ealauer/Animatronic_Research/Circuit Diagram Final/Circtuit Digram Camera.png

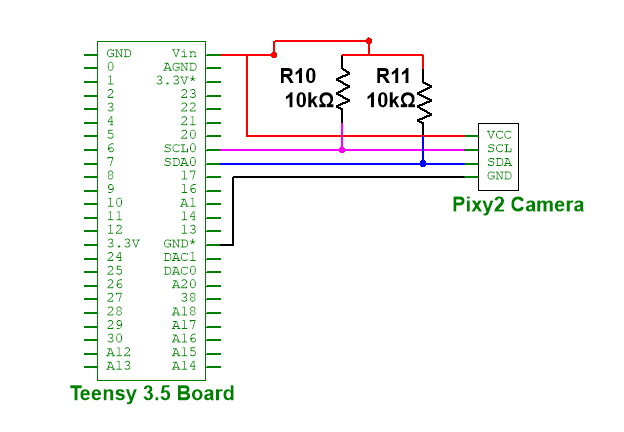
Circuit Diagram Final/Circtuit Digram Camera.png
