ealauer/Animatronic_Research/Circuit Diagram Final/Circuit Diagram FSR.png

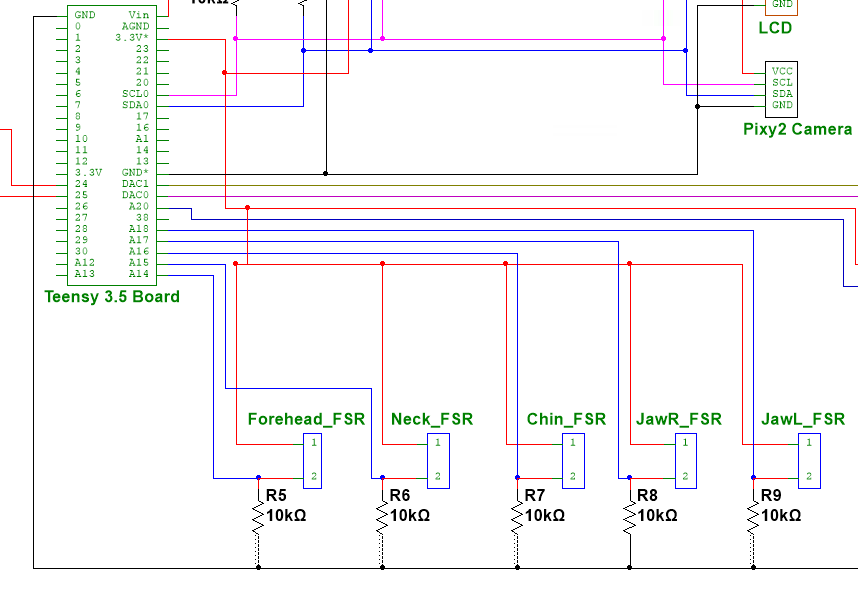
Circuit Diagram Final/Circuit Diagram FSR.png
