ealauer/Animatronic_Research/Circuit Diagram Final/Circuit Diagram Full1.png

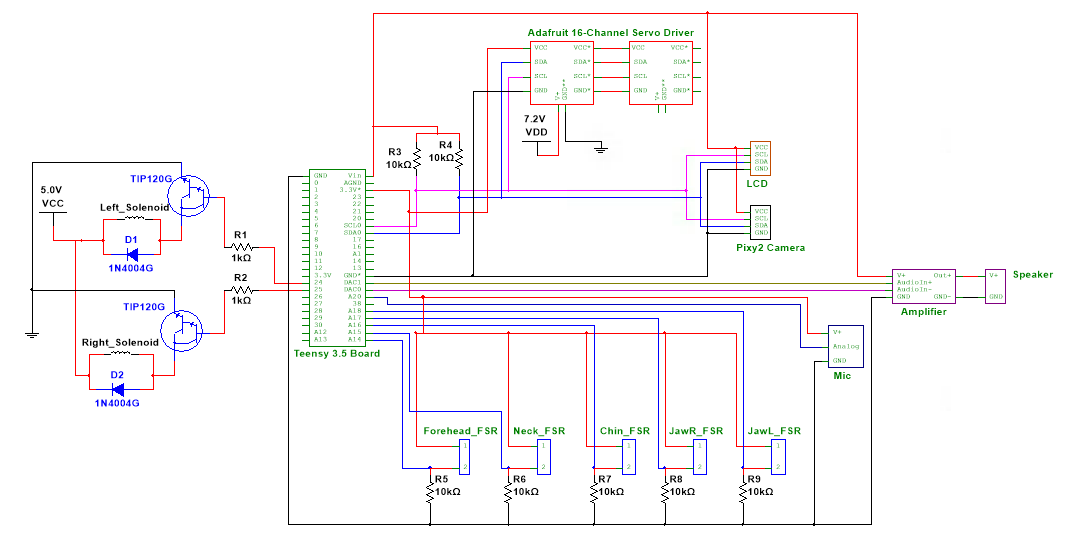
Circuit Diagram Final/Circuit Diagram Full1.png
