ealauer/Animatronic_Research/Circuit Diagram Final/Circuit Diagram I2C.png

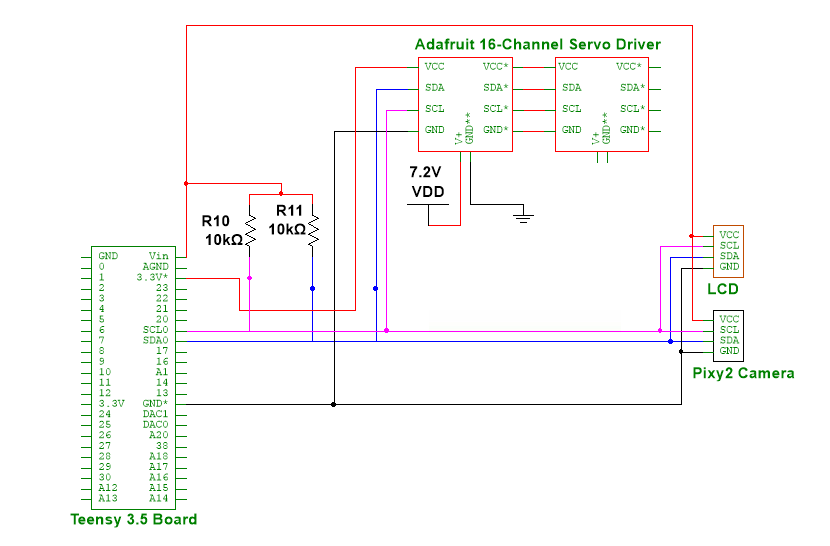
Circuit Diagram Final/Circuit Diagram I2C.png
