ealauer/Animatronic_Research/Circuit Diagram Final/Circuit Diagram LCD.png

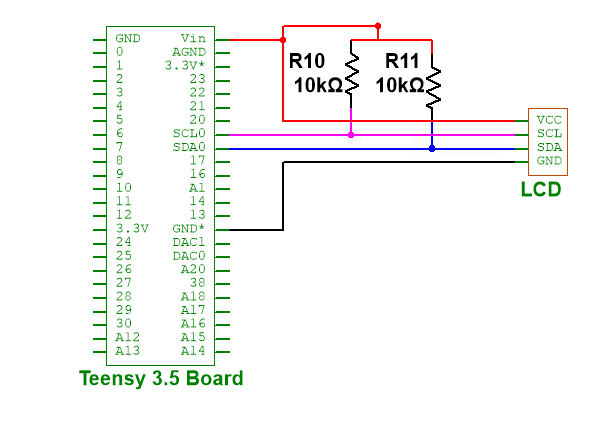
Circuit Diagram Final/Circuit Diagram LCD.png
