ealauer/Animatronic_Research/Circuit Diagram Final/Circuit Diagram MIC.png

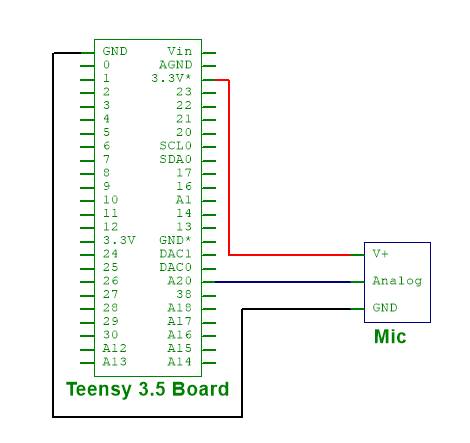
Circuit Diagram Final/Circuit Diagram MIC.png
