ealauer/Animatronic_Research/Circuit Diagram Final/Circuit Diagram Pulse.png

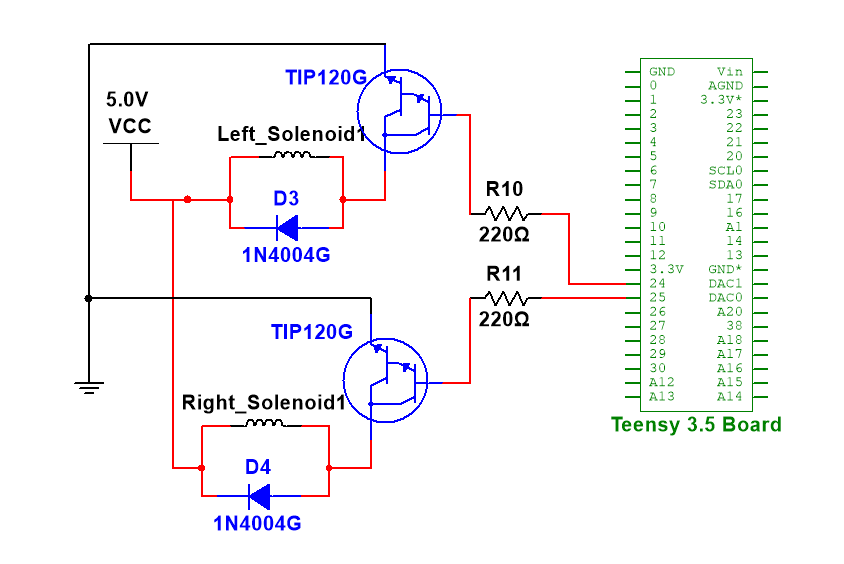
Circuit Diagram Final/Circuit Diagram Pulse.png
