ealauer/Animatronic_Research/Circuit Diagram Final/Circuit Diagram Servo.png

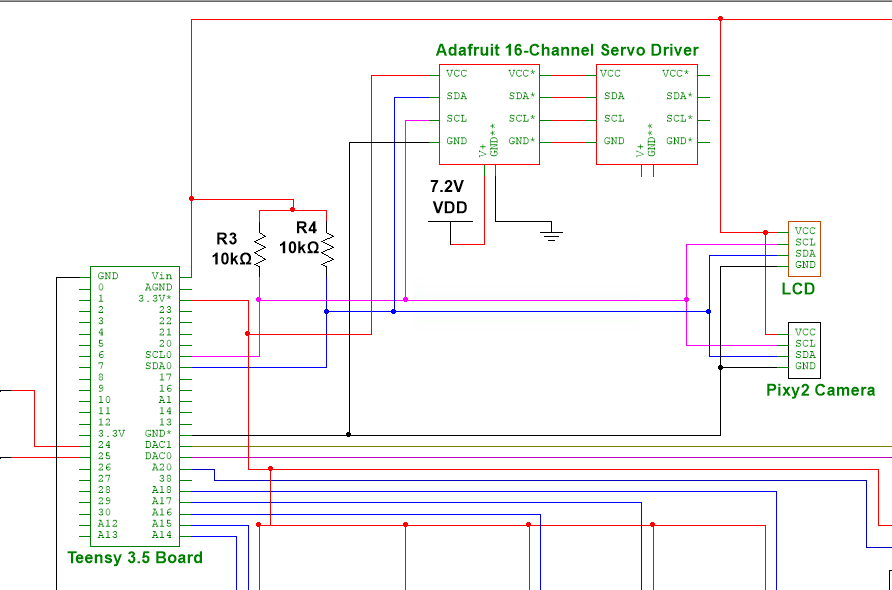
Circuit Diagram Final/Circuit Diagram Servo.png
