ealauer/Animatronic_Research/Circuit Diagram Final/Circuit Diagram Speaker.png

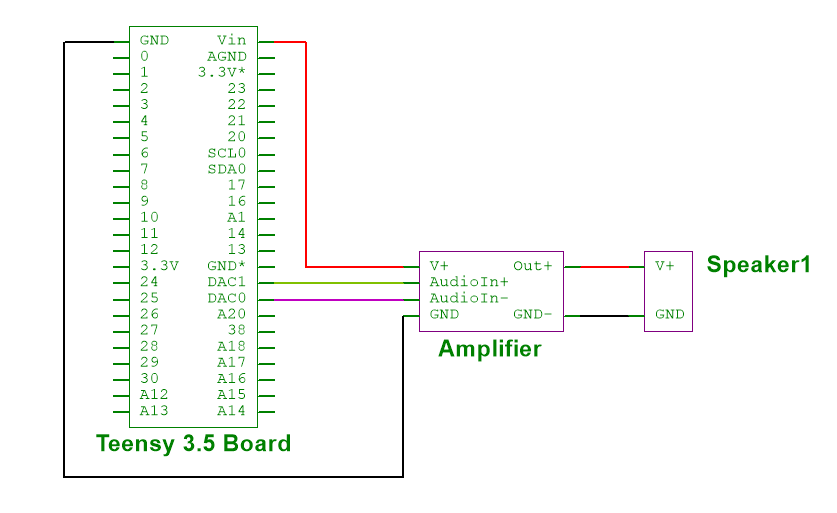
Circuit Diagram Final/Circuit Diagram Speaker.png
