ealauer/Animatronic_Research/MATLAB/figLegLengthWXPoseNew.png

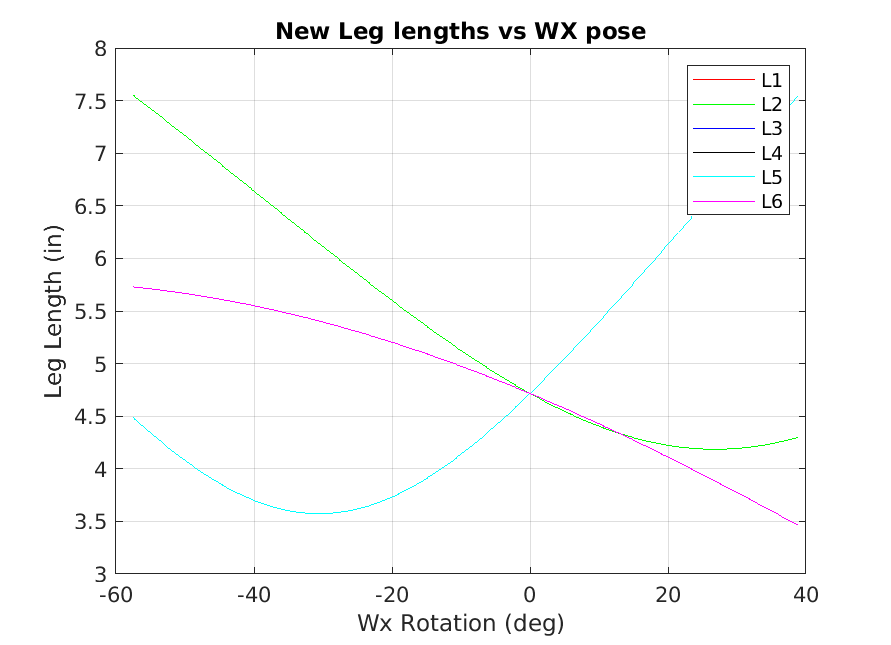
MATLAB/figLegLengthWXPoseNew.png
