ealauer/Animatronic_Research/MATLAB/figLegLengthWYPoseNew.png

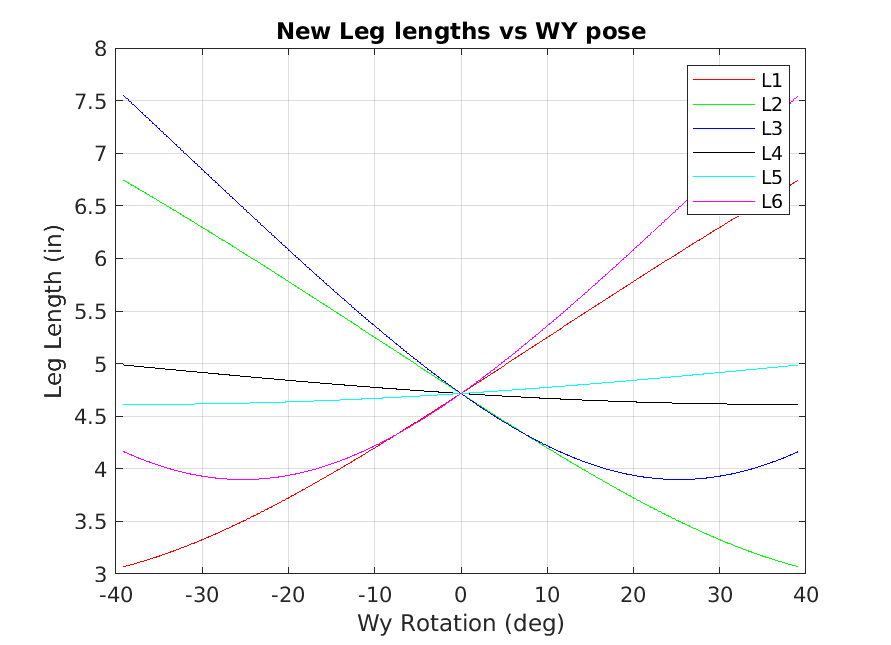
MATLAB/figLegLengthWYPoseNew.png
