ealauer/Animatronic_Research/MATLAB/figLegLengthWZPose.png

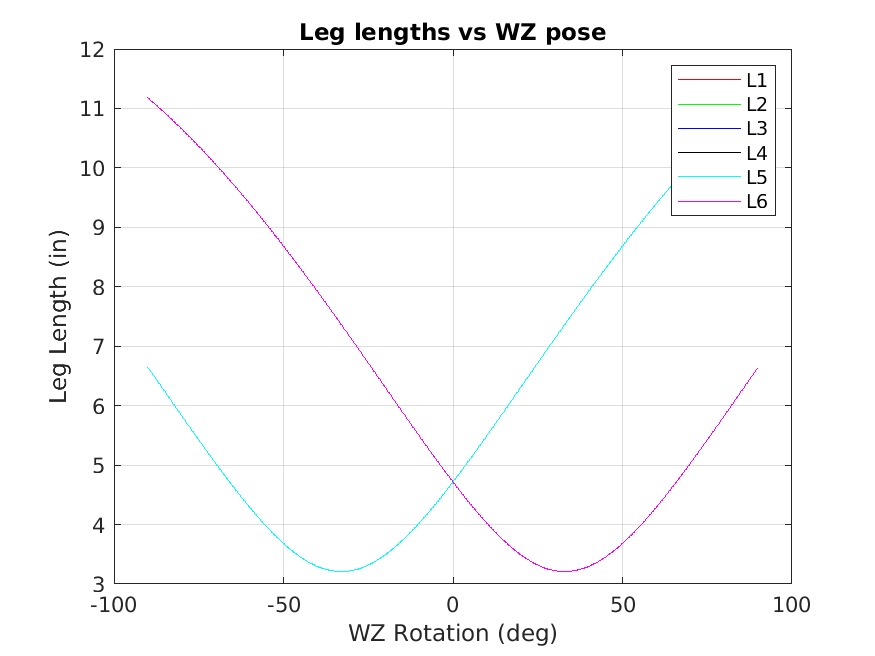
MATLAB/figLegLengthWZPose.png
