ealauer/Animatronic_Research/MATLAB/figLegLengthWZPoseNew.png

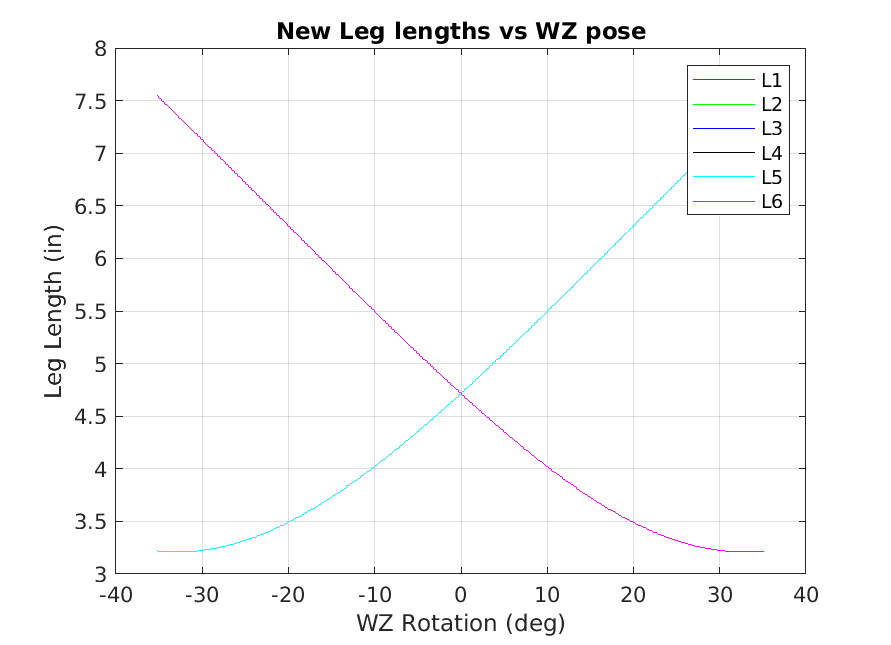
MATLAB/figLegLengthWZPoseNew.png
