ealauer/Animatronic_Research/MATLAB/figLegLengthZPose.png

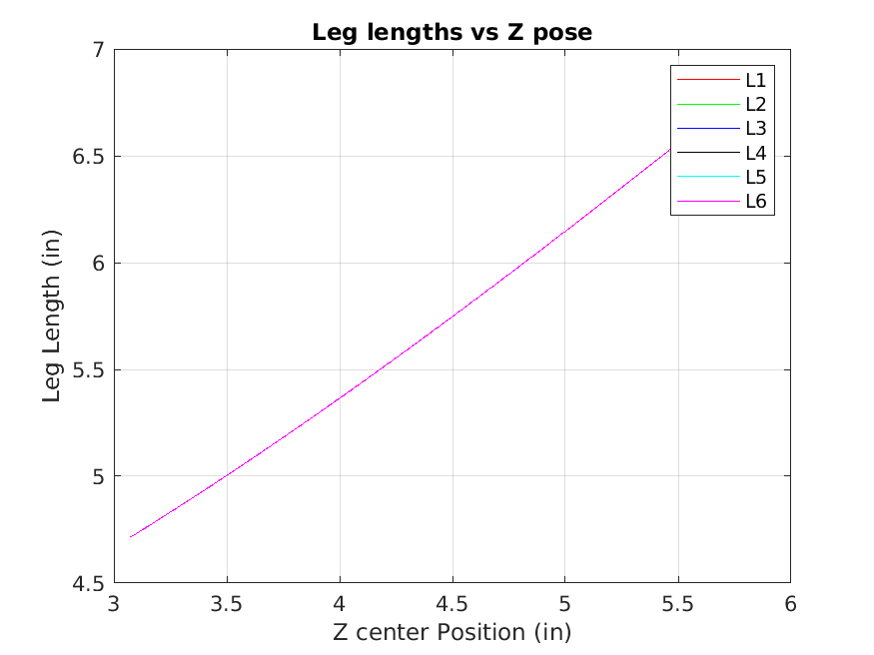
MATLAB/figLegLengthZPose.png
