ealauer/Animatronic_Research/MATLAB/figLegLengthZPoseNew.png

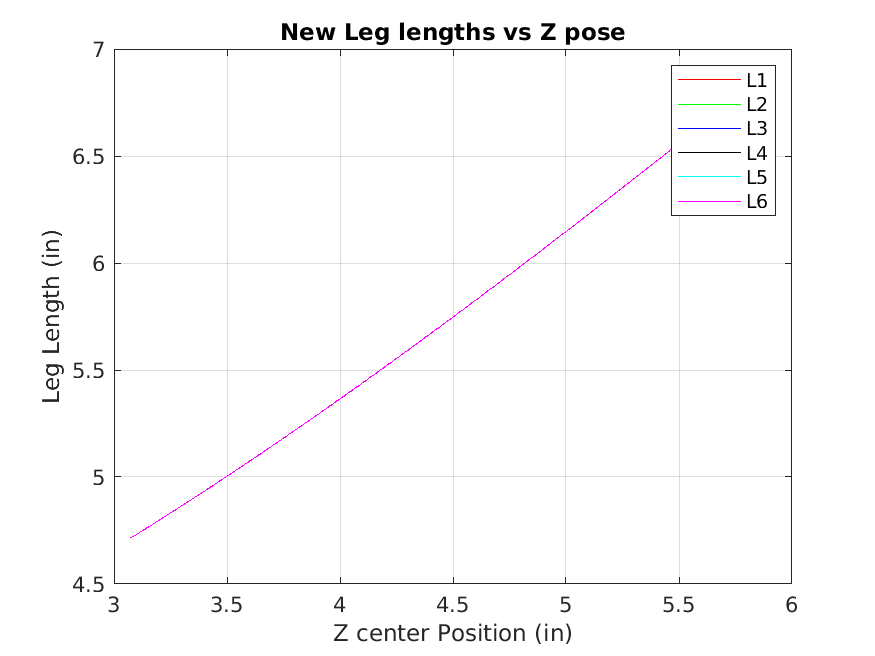
MATLAB/figLegLengthZPoseNew.png
