ealauer/Animatronic_Research/MATLAB/figServoWXPose.png

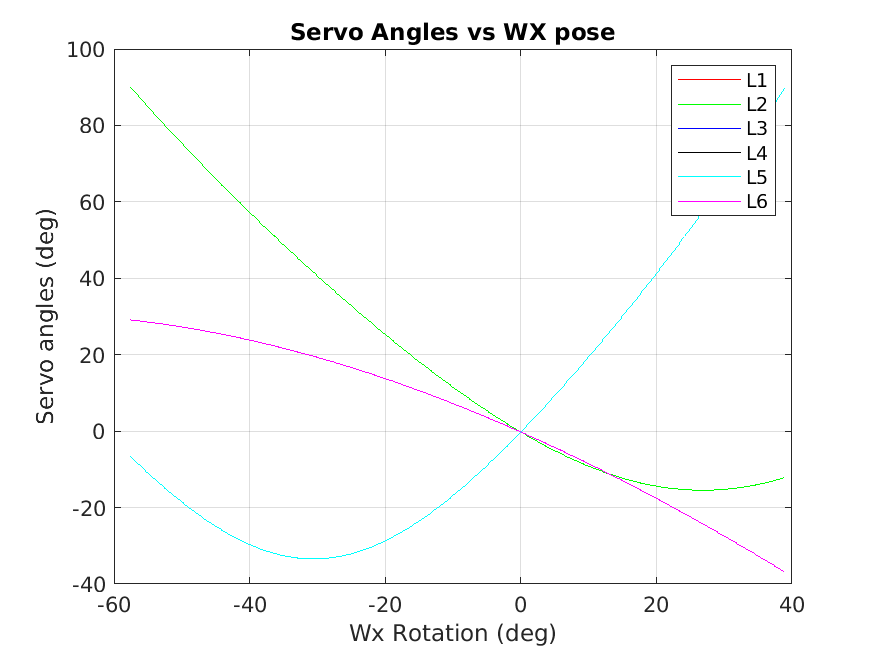
MATLAB/figServoWXPose.png
