ealauer/Animatronic_Research/MATLAB/figServoWYPose.png

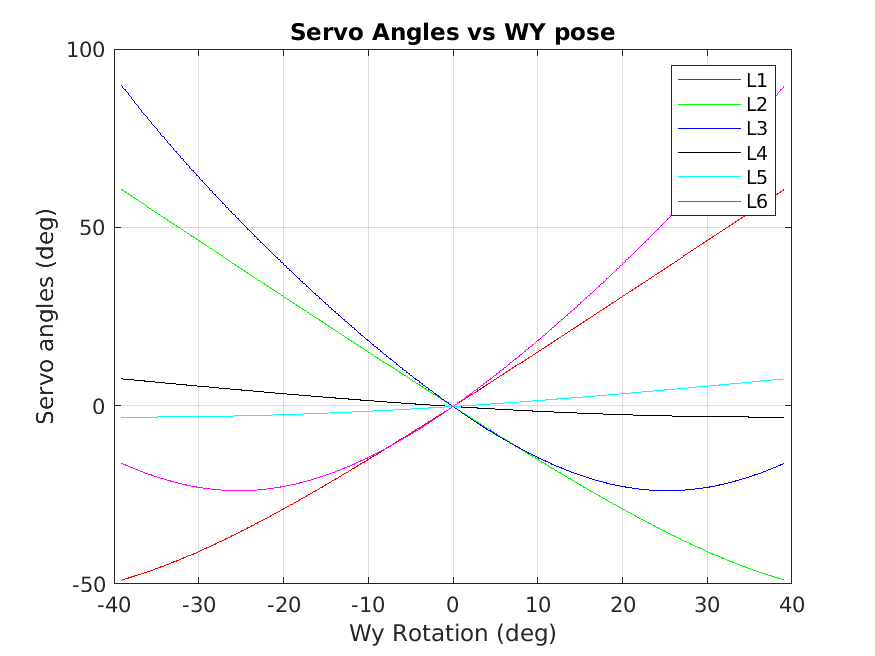
MATLAB/figServoWYPose.png
