ealauer/Animatronic_Research/MATLAB/figServoWZPose.png

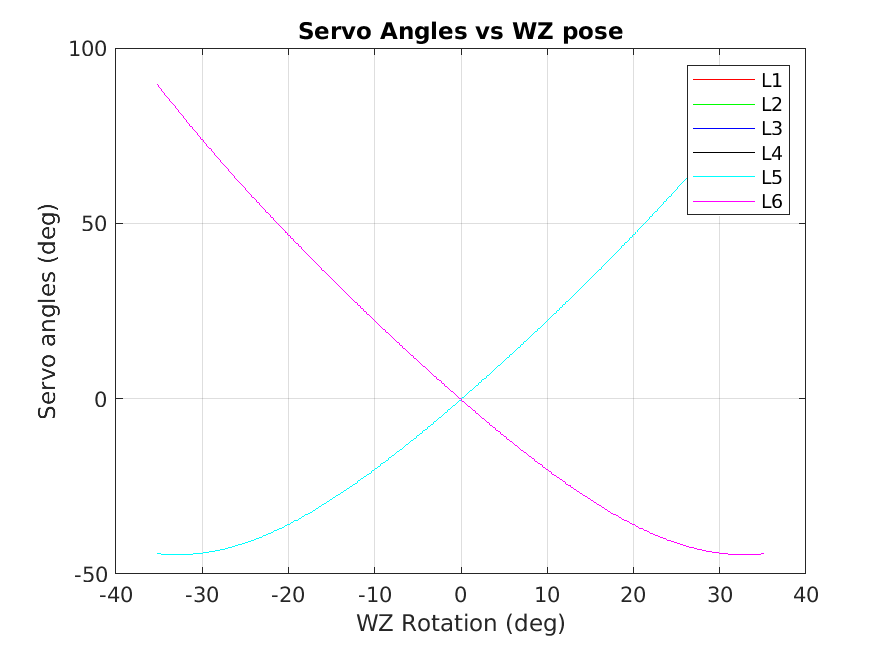
MATLAB/figServoWZPose.png
