ealauer/Animatronic_Research/UI Flow Pictures/2LOC.jpg

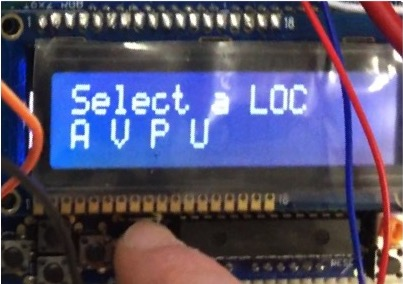
UI Flow Pictures/2LOC.jpg
