ealauer/Animatronic_Research/UI Flow Pictures/3LOCSet.jpg

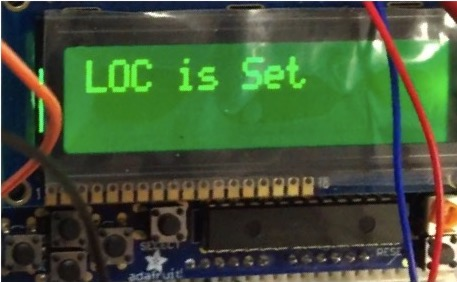
UI Flow Pictures/3LOCSet.jpg
