ealauer/Animatronic_Research/UI Flow Pictures/4Air.jpg

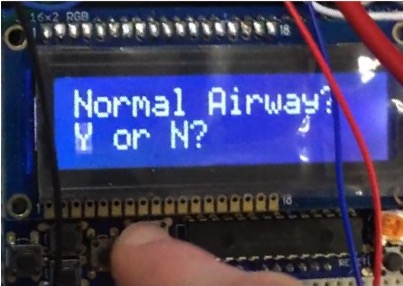
UI Flow Pictures/4Air.jpg
