ealauer/Animatronic_Research/UI Flow Pictures/7PulseInput.jpg

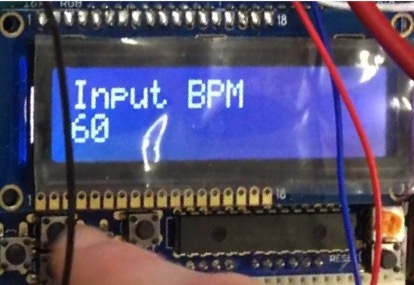
UI Flow Pictures/7PulseInput.jpg
