ealauer/Animatronic_Research/UI Flow Pictures/8PulseSet.jpg

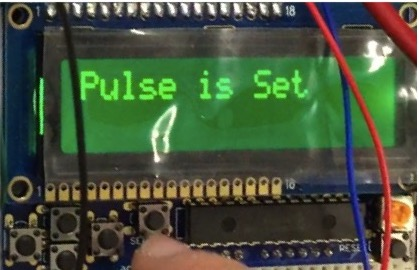
UI Flow Pictures/8PulseSet.jpg
