ealauer/Animatronic_Research/UI Flow Pictures/10StartQues.jpg

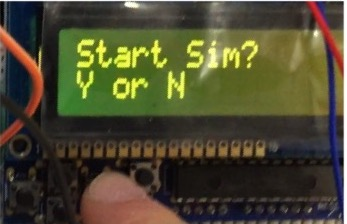
UI Flow Pictures/10StartQues.jpg
