ealauer/Animatronic_Research/UI Flow Pictures/11Change.jpg

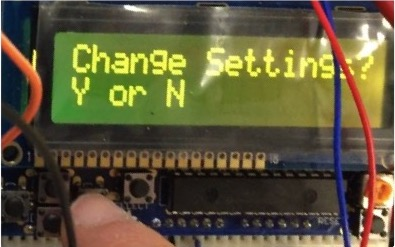
UI Flow Pictures/11Change.jpg
