ealauer/Animatronic_Research/UI Flow Pictures/12Start.jpg

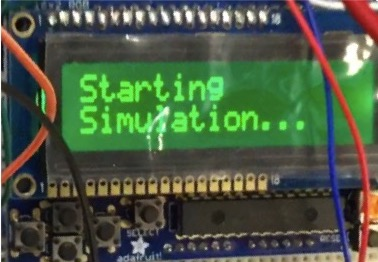
UI Flow Pictures/12Start.jpg
