ealauer/Animatronic_Research/SolidWorks Files/march16 eyebrow.SLDASM

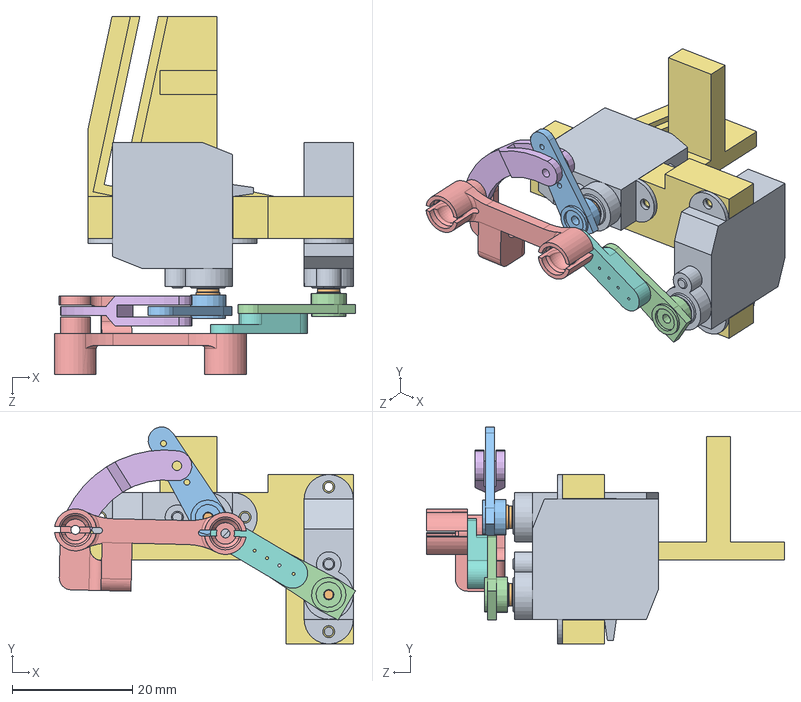
[picture p47: CAD file, 2021-04-09]
SolidWorks Files/march16 eyebrow.SLDASM
50.1 x 36.1 x 59.6 mm
D56MG Servo Case (1) x 2
D56MG Servo Shaft x 2
drilled and trimmed servo horn
Servo horn trimmed
brow link v2
middle link eyebrow v2
v9 eyebrowbaseleft
20mm extension link
