ealauer/Animatronic_Research/SolidWorks Files/Jaw/Jaw Thrust Linkage/LinkageAssemWithServoRight.SLDASM

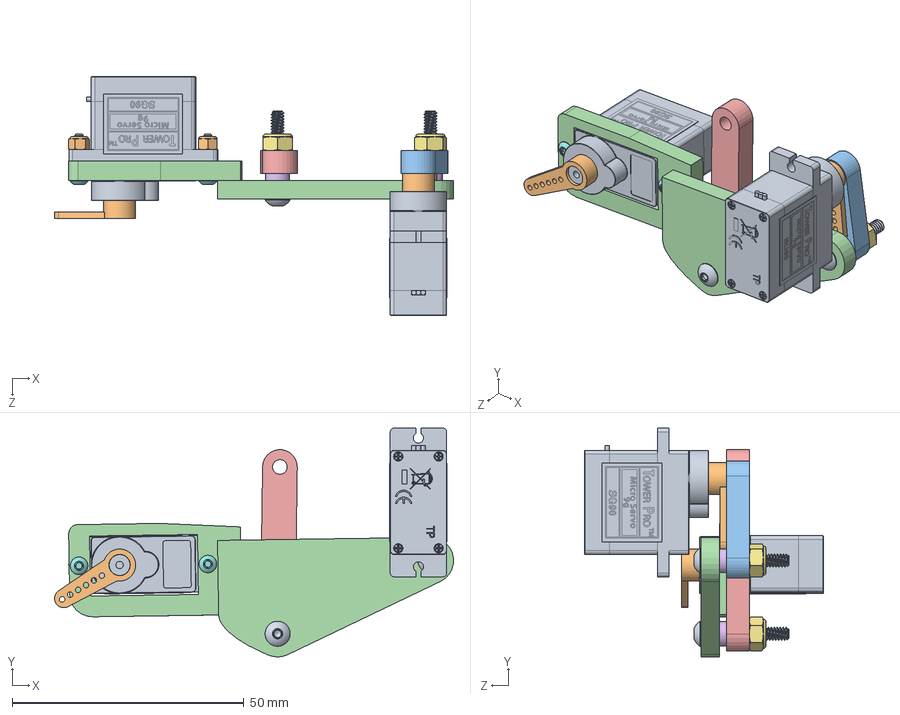
[picture p48: CAD file, 2021-04-09]
SolidWorks Files/Jaw/Jaw Thrust Linkage/LinkageAssemWithServoRight.SLDASM
86.1 x 49.4 x 51.7 mm
SG90 - Micro Servo 9g - Tower Pro.1 x 2
SG90 - Micro Servo 9g - Tower Pro.2 x 2
Driving
TriangleEditedRight
Driven2
90295A341_NYLON FLAT WASHER x 2
91831A005_TYPE 18-8 STAINLESS STL NYLON-INSERT LOCKNUT x 2
92095A104_BUTTON HEAD HEX DRIVE SCREW x 2
92949A113_18-8 SS BUTTON HEAD HEX DRIVE SCREW x 2
93625A101_TYPE 18-8 STAINLESS STL NYLON-INSERT LOCKNUT x 2
