ealauer/Animatronic_Research/SolidWorks Files/Eye CAD/Eye Assembly Final.SLDASM

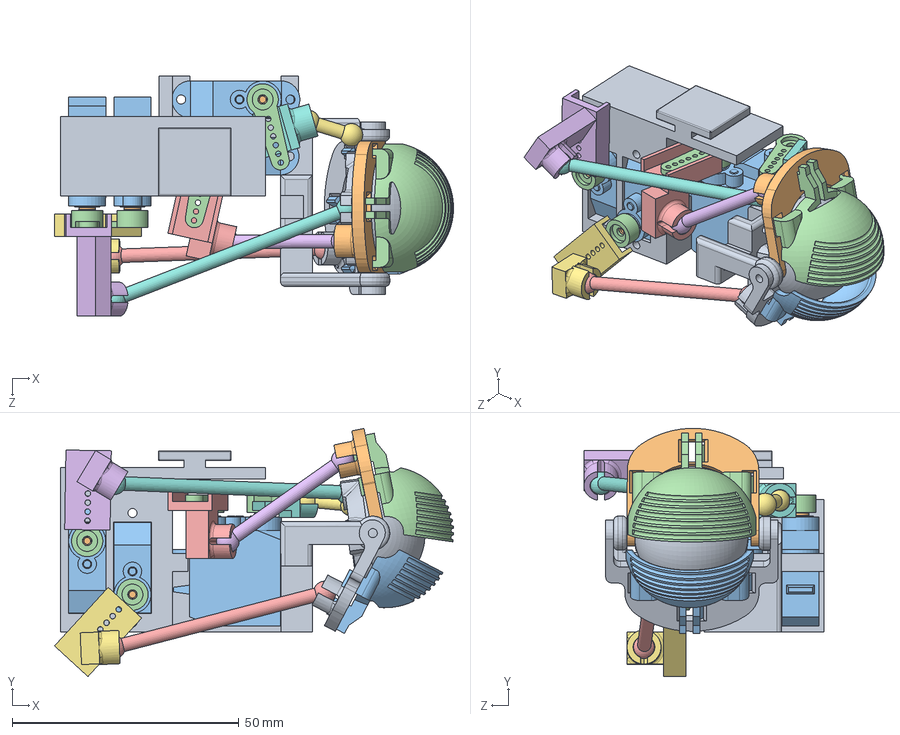
[picture p49: CAD file, 2021-04-09]
SolidWorks Files/Eye CAD/Eye Assembly Final.SLDASM
87.9 x 54.7 x 52.9 mm
final_eye_holder_V3.75_final
D56MG Servo Shaft x 4
D56MG Servo Case (1) x 4
SG90 - Micro Servo 9g - Tower Pro.2 x 4
final_servo_ball_joint_link4
final_servo_ball_joint_link3
final_servo_ball_joint_link2
final_servo_ball_joint_link1
final_eye clip butterfly bottom
final_eye clip butterfly top
final_clip on eyelid rev3
final_clip on eyelid top rev3
final_link1
final_link3
final_link4
final_link2
final eyeball
