ealauer/Animatronic_Research/SolidWorks Files/Neck/Neck Mechanism/Neck Lattice Assembly.SLDASM

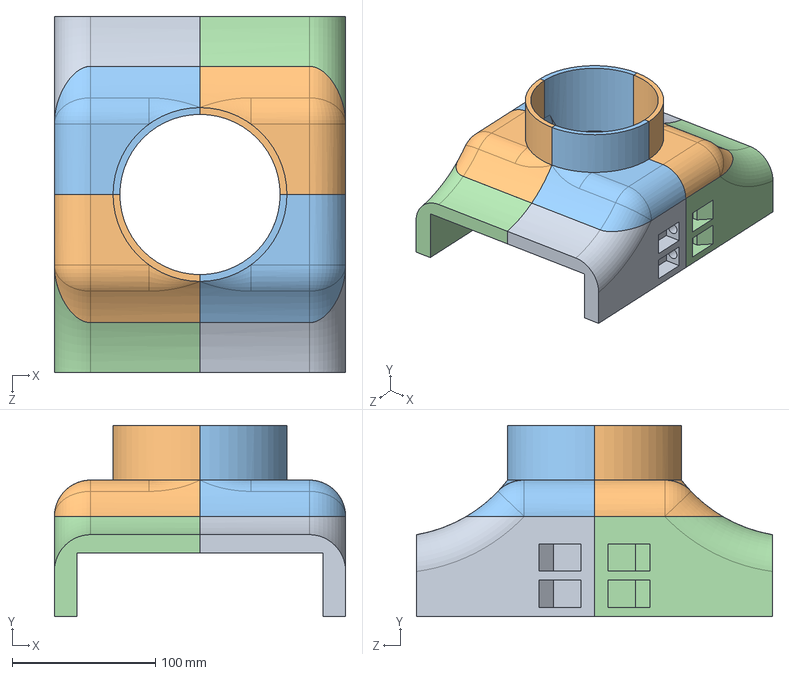
[picture p50: CAD file, 2021-04-09]
SolidWorks Files/Neck/Neck Mechanism/Neck Lattice Assembly.SLDASM
203.2 x 133.4 x 248.3 mm
Neck Sizing Bottom Female x 2
Neck Sizing Top FemaleMale x 2
Neck Sizing Top MaleMale x 2
Neck Sizing Bottom Male x 2
