ealauer/Animatronic_Research/SolidWorks Files/Eye Assembly.SLDASM

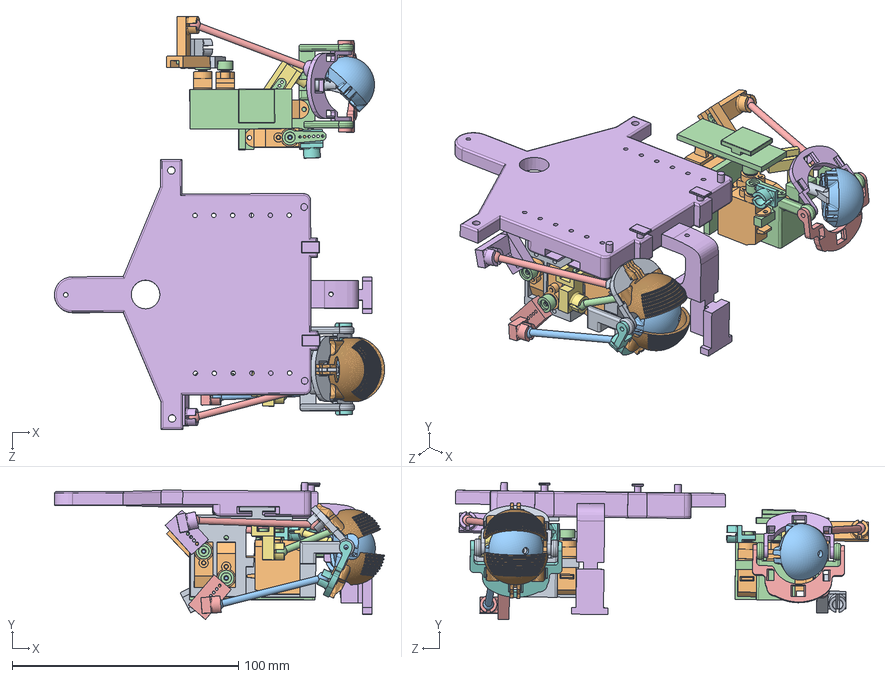
[picture p51: CAD file, 2021-04-09]
SolidWorks Files/Eye Assembly.SLDASM
146.1 x 60.7 x 182.7 mm
final_eye_holder_V3.75_final
D56MG Servo Case (1) x 8
D56MG Servo Shaft x 8
SG90 - Micro Servo 9g - Tower Pro.2 x 8
final_servo_ball_joint_link2
final_servo_ball_joint_link3
final_servo_ball_joint_link4
final_servo_ball_joint_link1
Ball Joint case x 2
Ball joint ball x 2
final_link1
final_link3
final_link2 x 2
platform_V3 (2)
new link
final_eye clip butterfly bottom
final_eye clip butterfly top
final_clip on eyelid top rev3 x 2
final eyeball_lauer x 2
final_left_eye_holder_lauer
final_left_eye clip butterfly bottom
final_left_eye clip butterfly top
final_left_servo_ball_joint_link4
final_left_servo_ball_joint_link1
final_left_servo_ball_joint_link2
final_left_servo_ball_joint_link3
