ealauer/Animatronic_Research/SolidWorks Files/Base Assembly.SLDASM

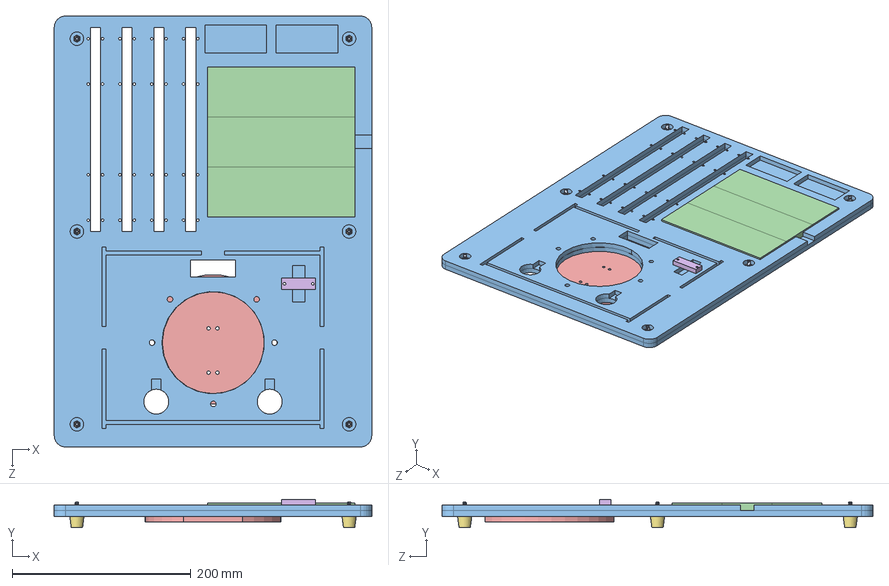
[picture p52: CAD file, 2021-04-09]
SolidWorks Files/Base Assembly.SLDASM
355.6 x 31.8 x 482.6 mm
90128A216_ZNC-PLTD ALLOY STL SCKT HEAD CAP SCREW x 6
90592A090_STEEL HEX NUT x 6
Base x 2
breadboard Updated x 3
Botttom Support
Cover
Stands x 6
