ealauer/Animatronic_Research/SolidWorks Files/D56MG Servo Assembly.SLDASM

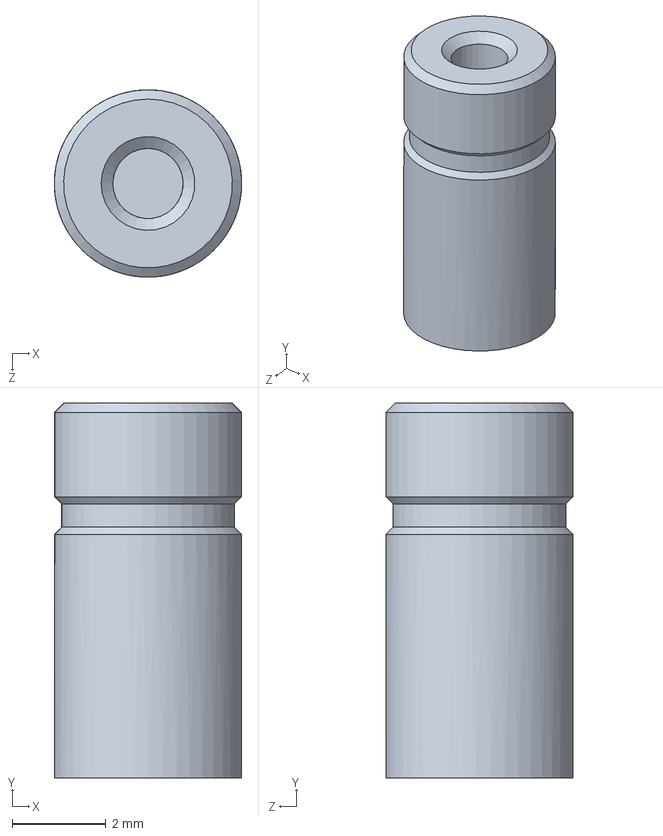
[picture p53: CAD file, 2021-04-09]
SolidWorks Files/D56MG Servo Assembly.SLDASM
4.00 x 8.00 x 4.00 mm
