ealauer/Animatronic_Research/SolidWorks Files/Eye CAD/final_eye clip butterfly bottom.SLDPRT

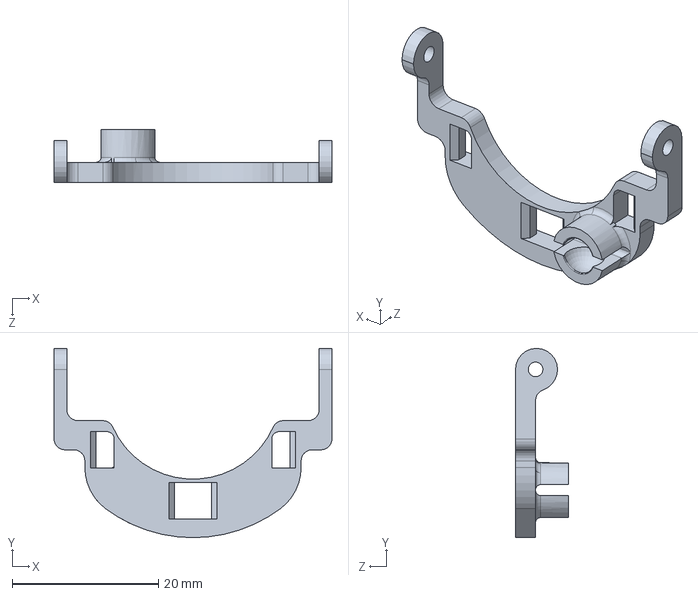
[picture p54: CAD file, 2021-04-09]
SolidWorks Files/Eye CAD/final_eye clip butterfly bottom.SLDPRT
38.0 x 25.9 x 7.25 mm
