ealauer/Animatronic_Research/SolidWorks Files/Eyebrows/Left Eyebrow/D56MG Servo Case.SLDPRT

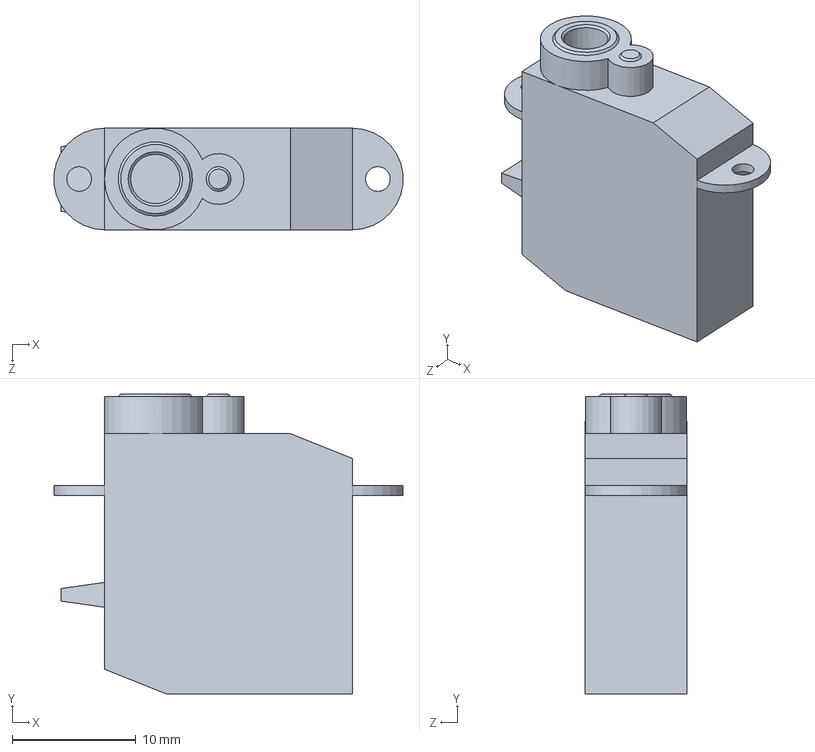
[picture p55: CAD file, 2021-04-09]
SolidWorks Files/Eyebrows/Left Eyebrow/D56MG Servo Case.SLDPRT
28.2 x 24.2 x 8.20 mm
