ealauer/Animatronic_Research/SolidWorks Files/Eyebrows/Left Eyebrow/Left .stl_s/brow link v2.STL

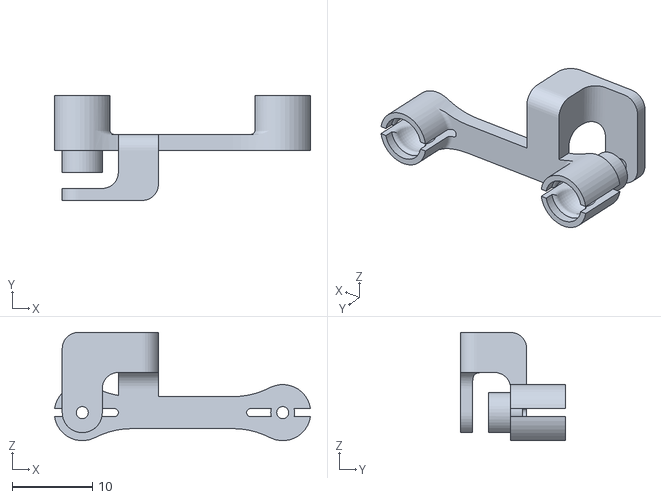
[picture p56: CAD file, 2021-04-09]
SolidWorks Files/Eyebrows/Left Eyebrow/Left .stl_s/brow link v2.STL
31.9 x 13.1 x 13.5
