ealauer/Animatronic_Research/SolidWorks Files/Eyebrows/Right Eyebrow/Right .stl_s/R_20mm extension link.STL

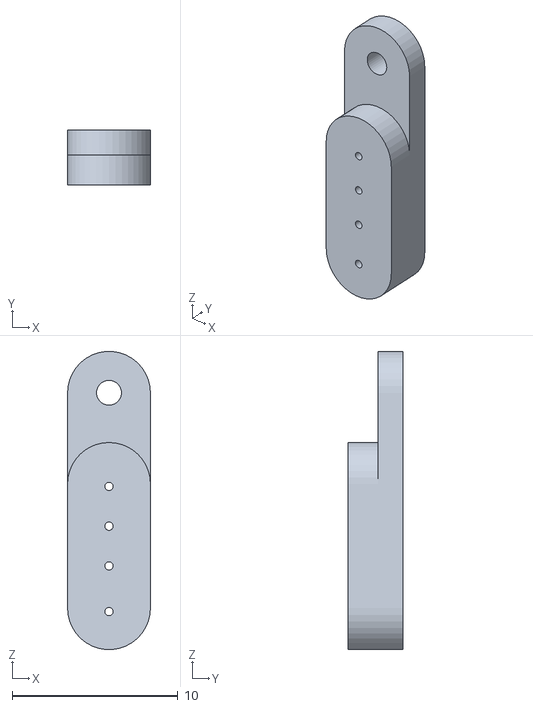
[picture p57: CAD file, 2021-04-09]
SolidWorks Files/Eyebrows/Right Eyebrow/Right .stl_s/R_20mm extension link.STL
5.00 x 3.30 x 18.0
