ealauer/Animatronic_Research/SolidWorks Files/final_servo_ball_joint_link1.SLDPRT

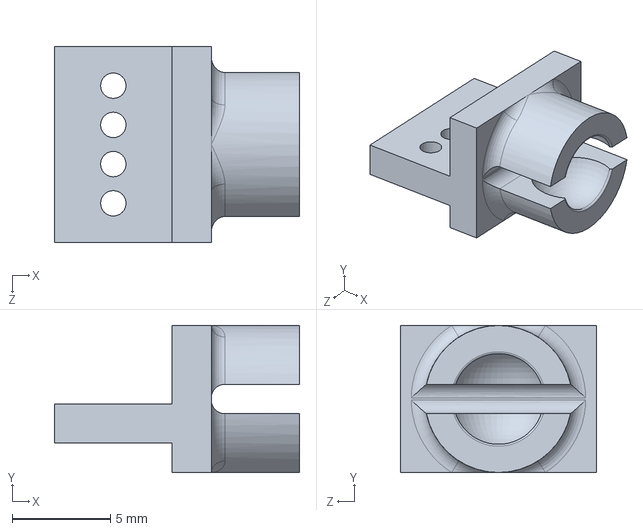
[picture p58: CAD file, 2021-04-09]
SolidWorks Files/final_servo_ball_joint_link1.SLDPRT
12.5 x 7.50 x 10.0 mm
