ealauer/Animatronic_Research/SolidWorks Files/Jaw/Oral Roof.SLDPRT

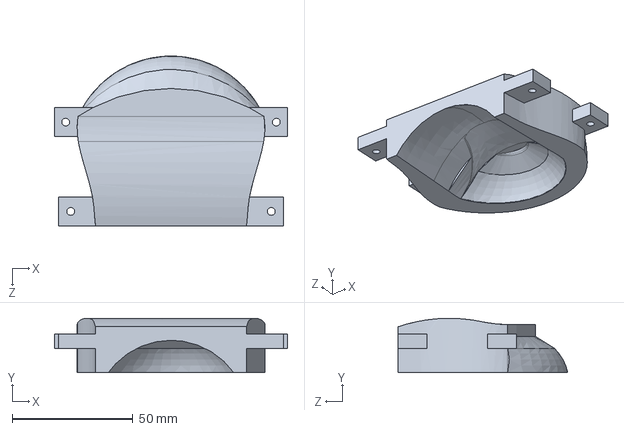
[picture p59: CAD file, 2021-04-09]
SolidWorks Files/Jaw/Oral Roof.SLDPRT
96.6 x 22.5 x 70.4 mm
