ealauer/Animatronic_Research/SolidWorks Files/Neck/Neck Enclosure/Cover.SLDPRT

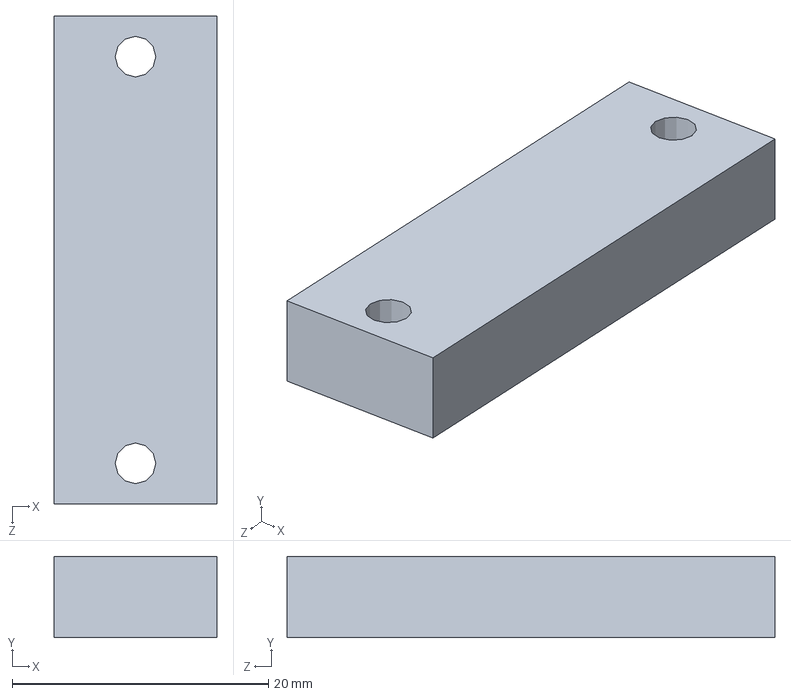
[picture p60: CAD file, 2021-04-09]
SolidWorks Files/Neck/Neck Enclosure/Cover.SLDPRT
12.7 x 6.35 x 38.1 mm
