ealauer/Animatronic_Research/SolidWorks Files/Neck/Neck Mechanism/Servo Linkage1.SLDPRT

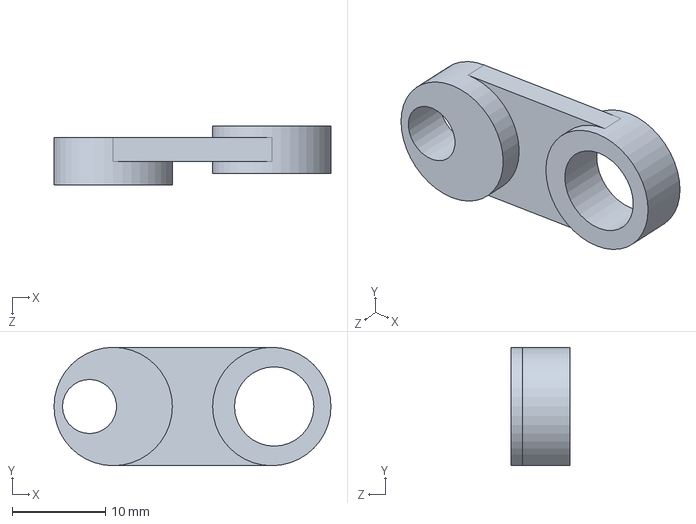
[picture p61: CAD file, 2021-04-09]
SolidWorks Files/Neck/Neck Mechanism/Servo Linkage1.SLDPRT
29.7 x 12.7 x 6.35 mm
