ealauer/Animatronic_Research/Stewart Platform Initial Designs/workspace modeling.SLDPRT

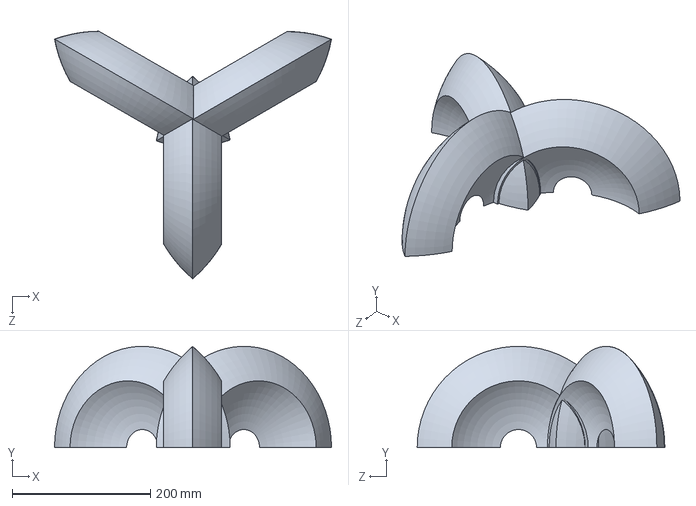
[picture p62: CAD file, 2021-04-09]
Stewart Platform Initial Designs/workspace modeling.SLDPRT
401.2 x 146.7 x 358.7 mm
