ealauer/Animatronic_Research/SolidWorks Files/Eyebrows/Left Eyebrow/Left .stl_s/v9 eyebrowbaseleft.STL

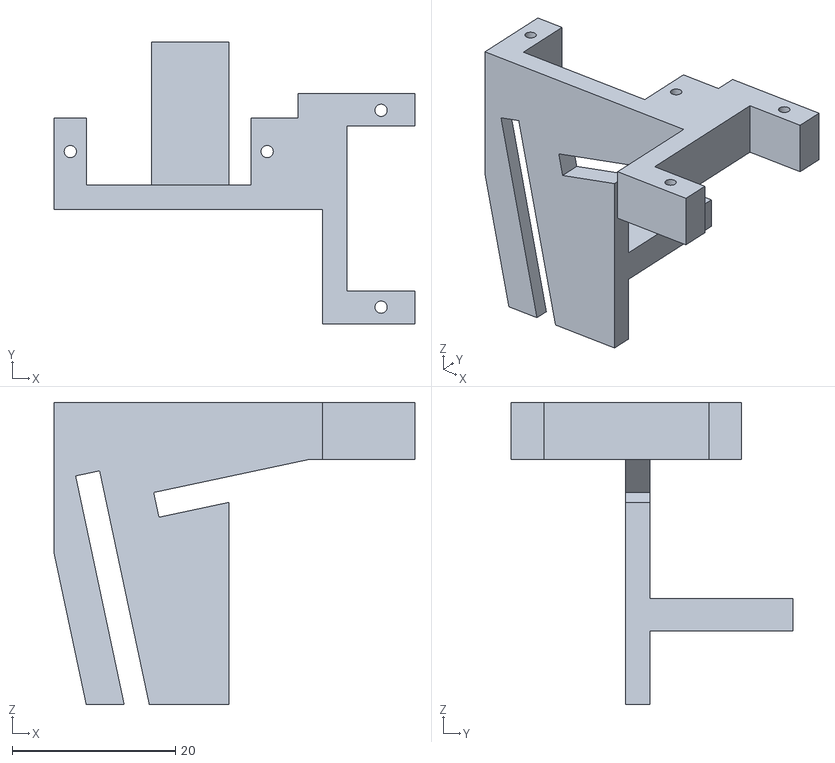
[picture p63: CAD file, 2021-04-09]
SolidWorks Files/Eyebrows/Left Eyebrow/Left .stl_s/v9 eyebrowbaseleft.STL
44.2 x 34.5 x 37.0
