ealauer/Animatronic_Research/SolidWorks Files/Gasket Rod.SLDPRT

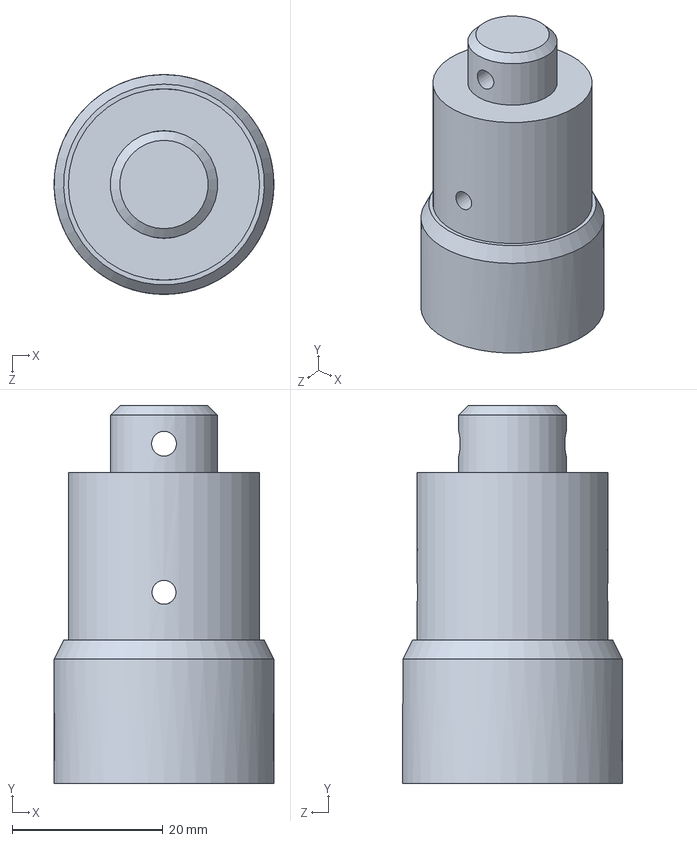
[picture p64: CAD file, 2021-04-09]
SolidWorks Files/Gasket Rod.SLDPRT
29.2 x 50.2 x 29.2 mm
