ealauer/Animatronic_Research/SolidWorks Files/Jaw/Jaw Thrust Linkage/Driven2.SLDPRT

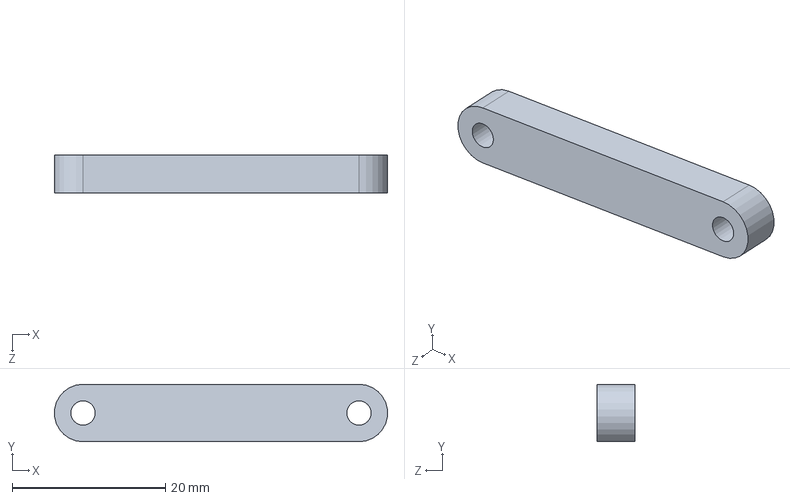
[picture p65: CAD file, 2021-04-09]
SolidWorks Files/Jaw/Jaw Thrust Linkage/Driven2.SLDPRT
43.4 x 7.50 x 5.00 mm
