ealauer/Animatronic_Research/SolidWorks Files/Neck/Neck Mechanism/Savr.SLDPRT

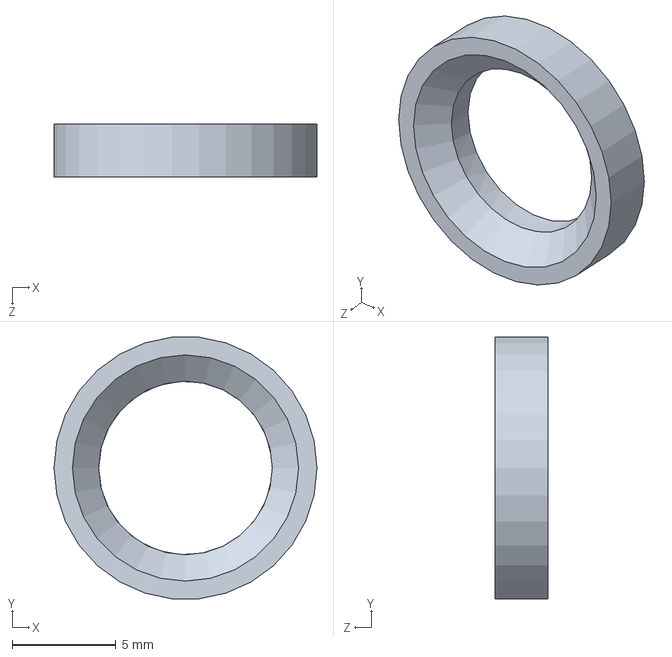
[picture p67: CAD file, 2021-04-09]
SolidWorks Files/Neck/Neck Mechanism/Savr.SLDPRT
12.7 x 12.6 x 2.54 mm
