ealauer/Animatronic_Research/Stewart Platform Initial Designs/platform_bot.dxf

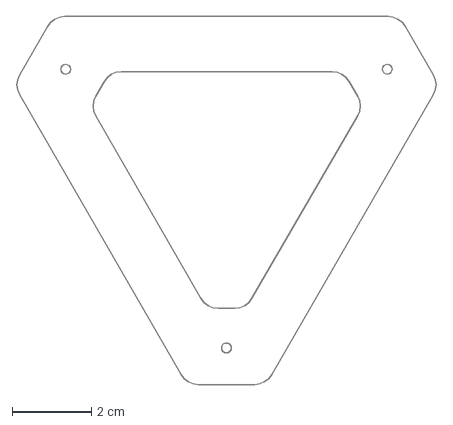
[picture p68: CAD file, 2021-04-09]
Stewart Platform Initial Designs/platform_bot.dxf
10.6 x 9.31 cm
