ealauer/Animatronic_Research/SolidWorks Files/Eyebrows/Left Eyebrow/Left .stl_s/middle link eyebrow v2.STL

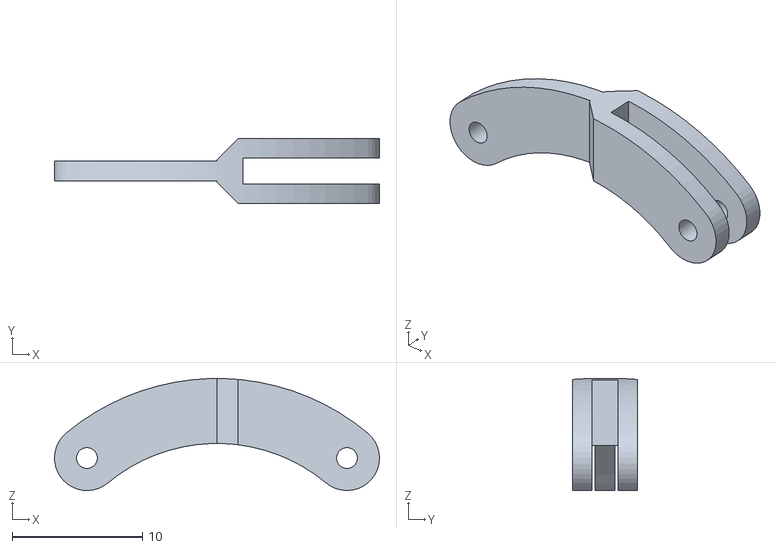
[picture p69: CAD file, 2021-04-09]
SolidWorks Files/Eyebrows/Left Eyebrow/Left .stl_s/middle link eyebrow v2.STL
25.0 x 5.00 x 8.62
