ealauer/Animatronic_Research/SolidWorks Files/Eyebrows/Left Eyebrow/Servo horn trimmed.SLDPRT

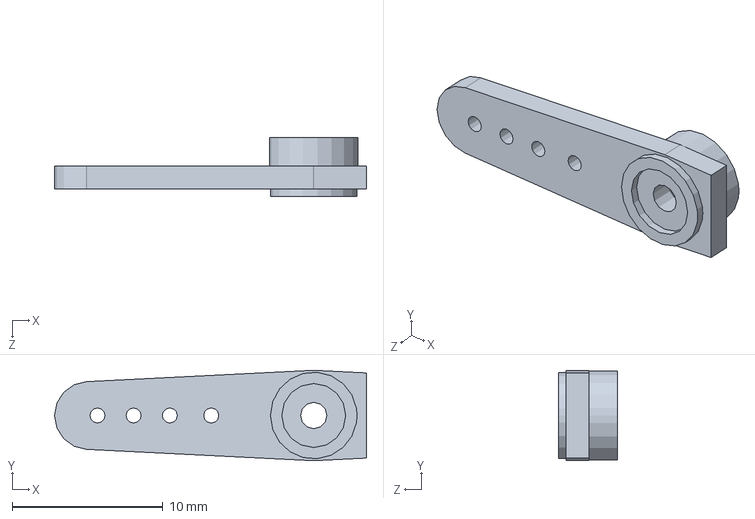
[picture p70: CAD file, 2021-04-09]
SolidWorks Files/Eyebrows/Left Eyebrow/Servo horn trimmed.SLDPRT
20.7 x 6.00 x 3.90 mm
