ealauer/Animatronic_Research/SolidWorks Files/Jaw/Jaw Thrust Linkage/Driving.SLDPRT

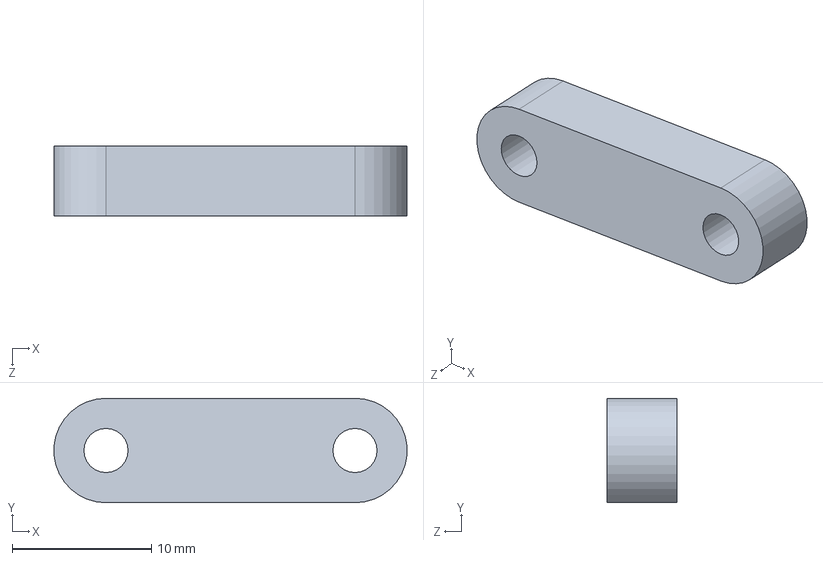
[picture p71: CAD file, 2021-04-09]
SolidWorks Files/Jaw/Jaw Thrust Linkage/Driving.SLDPRT
25.3 x 7.50 x 5.00 mm
