ealauer/Animatronic_Research/SolidWorks Files/Jaw/Tongue 2.SLDPRT

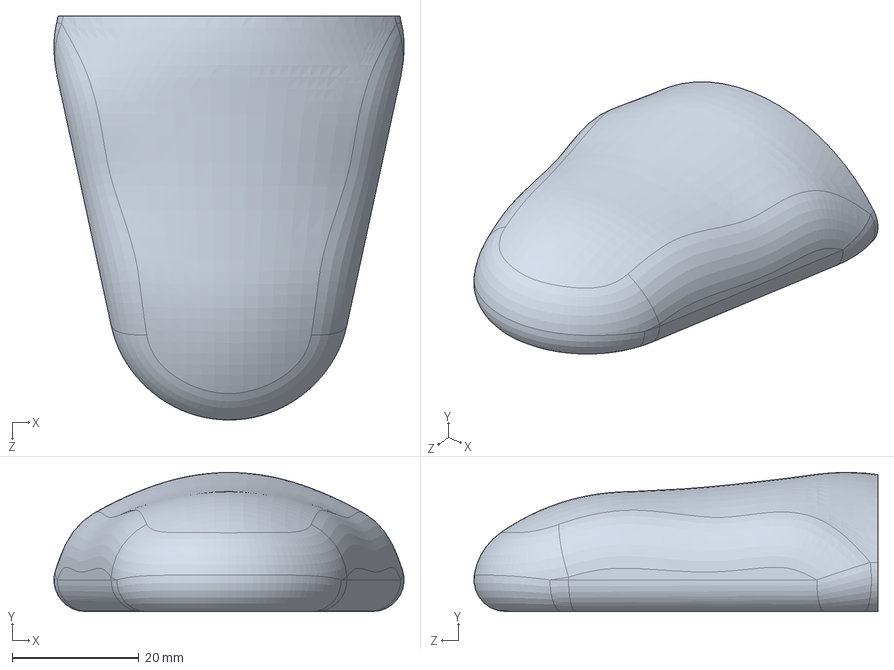
[picture p72: CAD file, 2021-04-09]
SolidWorks Files/Jaw/Tongue 2.SLDPRT
55.3 x 22.0 x 63.8 mm
