ealauer/Animatronic_Research/SolidWorks Files/Neck/Neck Enclosure/Top Actual.SLDPRT

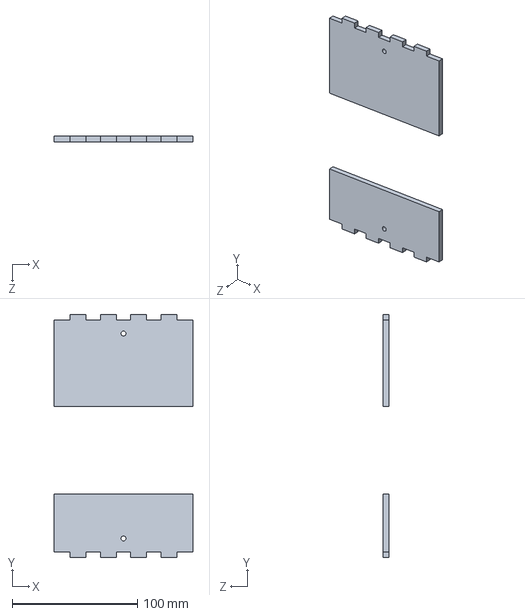
[picture p73: CAD file, 2021-04-09]
SolidWorks Files/Neck/Neck Enclosure/Top Actual.SLDPRT
110.9 x 194.2 x 4.50 mm
