ealauer/Animatronic_Research/SolidWorks Files/Neck/Neck Mechanism/Gasket to HeadNeck Interface Rod.SLDPRT

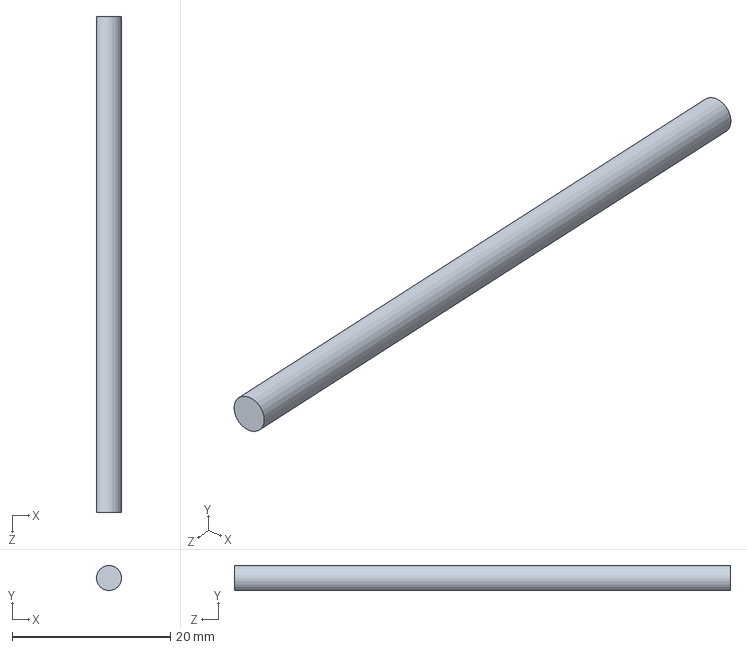
[picture p74: CAD file, 2021-04-09]
SolidWorks Files/Neck/Neck Mechanism/Gasket to HeadNeck Interface Rod.SLDPRT
3.17 x 3.17 x 62.7 mm
