ealauer/Animatronic_Research/Stewart Platform Initial Designs/platform_top.dxf

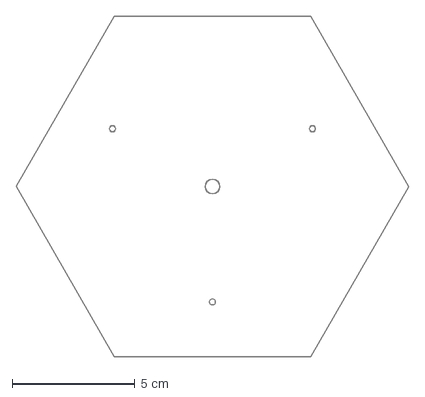
[picture p75: CAD file, 2021-04-09]
Stewart Platform Initial Designs/platform_top.dxf
16.0 x 13.9 cm
