ealauer/Animatronic_Research/SolidWorks Files/Eye CAD/final_clip on eyelid top rev3.SLDPRT

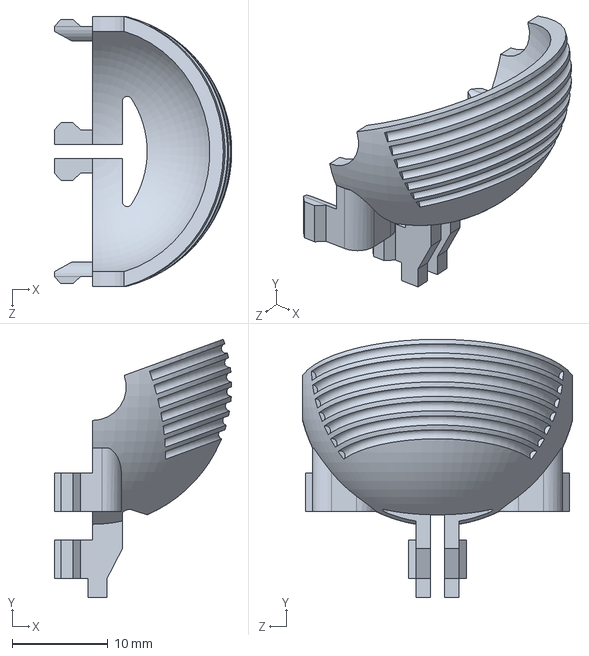
[picture p76: CAD file, 2021-04-09]
SolidWorks Files/Eye CAD/final_clip on eyelid top rev3.SLDPRT
18.5 x 26.9 x 28.1 mm
