ealauer/Animatronic_Research/SolidWorks Files/Jaw/sg90-micro-servo-9g-tower-pro-1.snapshot.3/SG90 - Micro Servo 9g - Tower Pro.3.SLDPRT

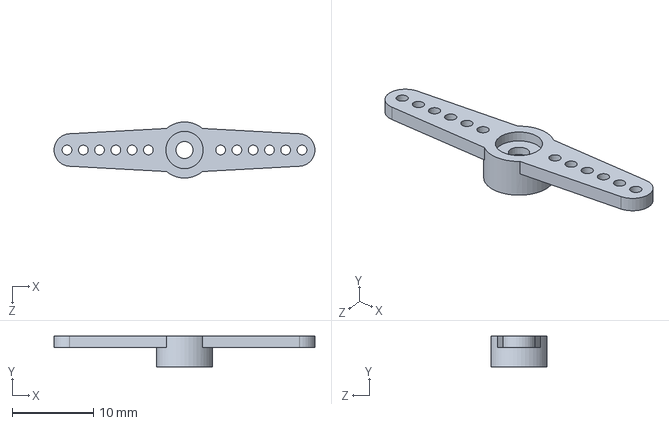
[picture p77: CAD file, 2021-04-09]
SolidWorks Files/Jaw/sg90-micro-servo-9g-tower-pro-1.snapshot.3/SG90 - Micro Servo 9g - Tower Pro.3.SLDPRT
32.1 x 3.80 x 6.90 mm
