ealauer/Animatronic_Research/SolidWorks Files/Jaw/Trachea 2.SLDPRT

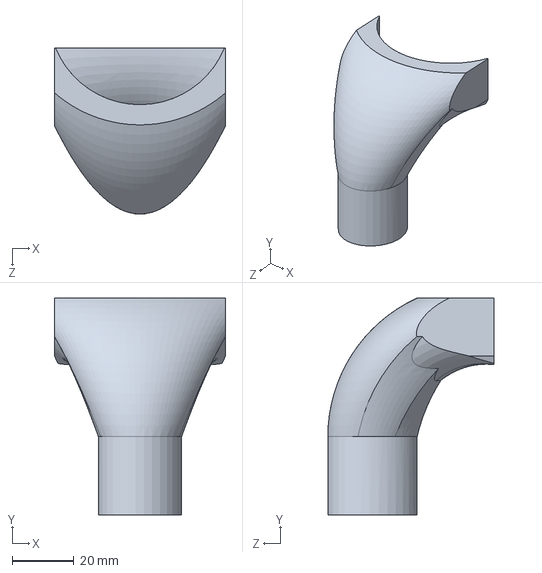
[picture p78: CAD file, 2021-04-09]
SolidWorks Files/Jaw/Trachea 2.SLDPRT
55.6 x 70.4 x 53.9 mm
