ealauer/Animatronic_Research/SolidWorks Files/Neck/Neck Mechanism/Ball Rod.SLDPRT

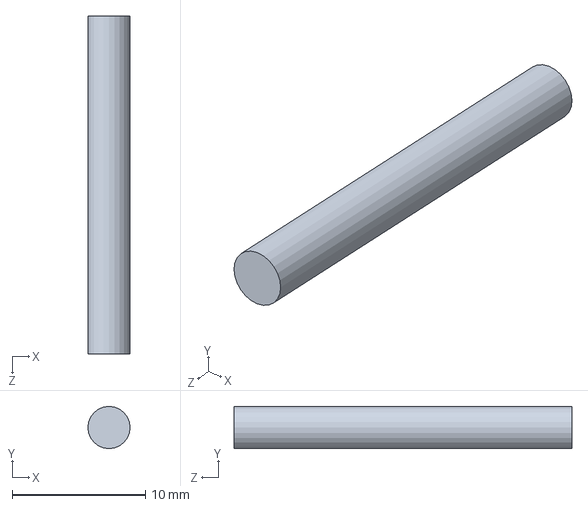
[picture p79: CAD file, 2021-04-09]
SolidWorks Files/Neck/Neck Mechanism/Ball Rod.SLDPRT
3.17 x 3.17 x 25.4 mm
