ealauer/Animatronic_Research/Stewart Platform Initial Designs/rod.SLDPRT

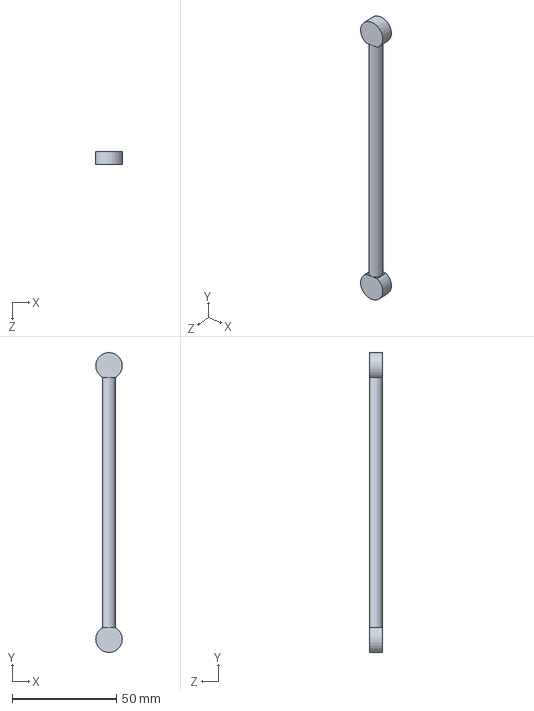
[picture p80: CAD file, 2021-04-09]
Stewart Platform Initial Designs/rod.SLDPRT
12.7 x 143.6 x 6.35 mm
