ealauer/Animatronic_Research/SolidWorks Files/Eye CAD/final left butterfly top.SLDPRT

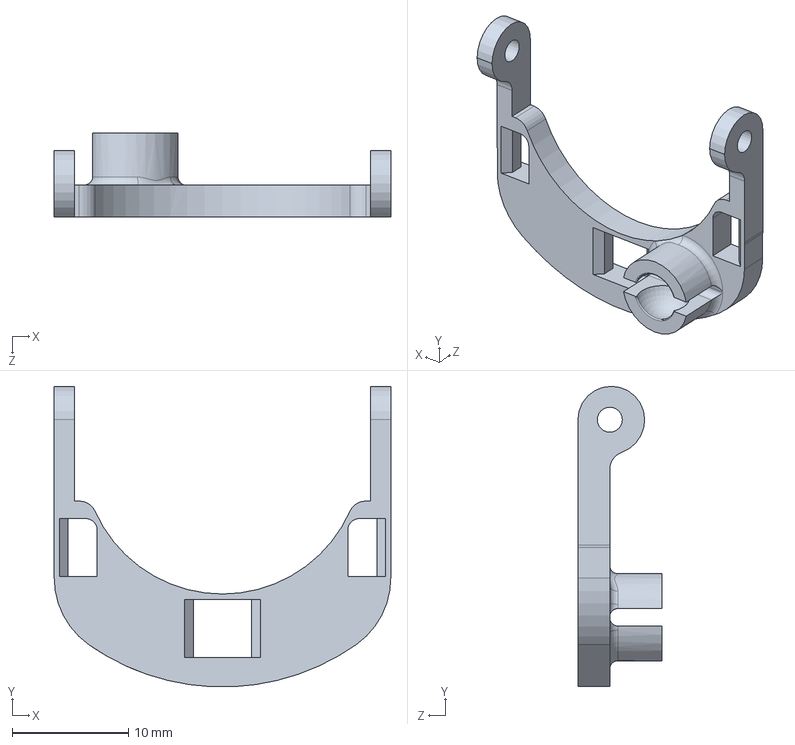
[picture p81: CAD file, 2021-04-09]
SolidWorks Files/Eye CAD/final left butterfly top.SLDPRT
29.0 x 25.9 x 7.25 mm
