ealauer/Animatronic_Research/SolidWorks Files/Jaw/Jawbone 3.SLDPRT

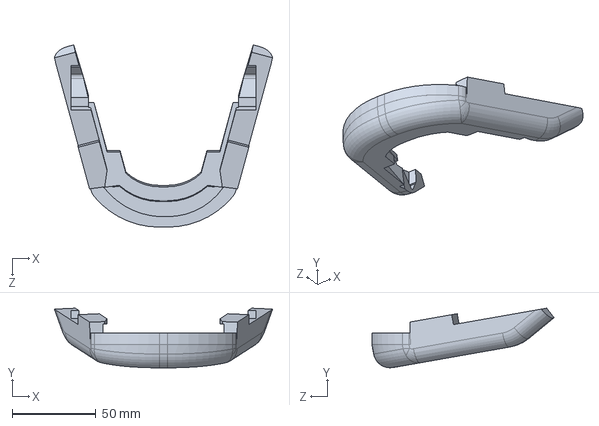
[picture p82: CAD file, 2021-04-09]
SolidWorks Files/Jaw/Jawbone 3.SLDPRT
130.0 x 35.6 x 108.7 mm
