ealauer/Animatronic_Research/SolidWorks Files/Jaw/sg90-micro-servo-9g-tower-pro-1.snapshot.3/SG90 - Micro Servo 9g - Tower Pro.6.SLDPRT

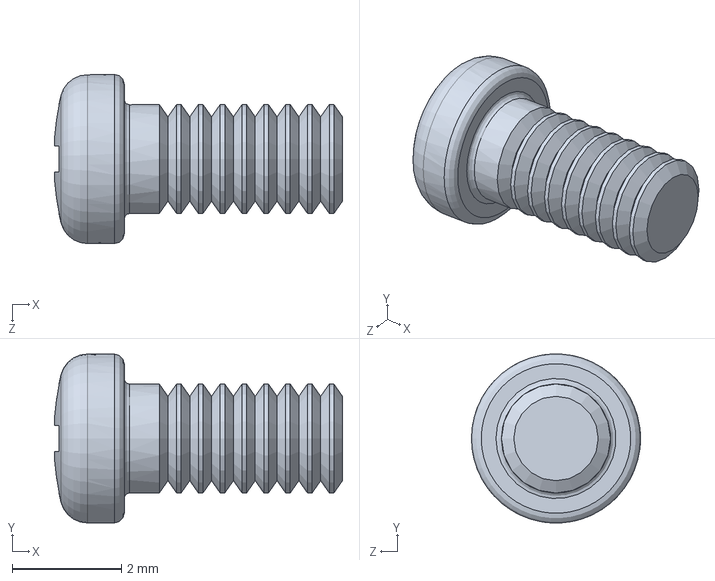
[picture p83: CAD file, 2021-04-09]
SolidWorks Files/Jaw/sg90-micro-servo-9g-tower-pro-1.snapshot.3/SG90 - Micro Servo 9g - Tower Pro.6.SLDPRT
5.28 x 3.10 x 3.10 mm
