ealauer/Animatronic_Research/SolidWorks Files/Neck/Neck Mechanism/Neck Sizing Bottom Male.SLDPRT

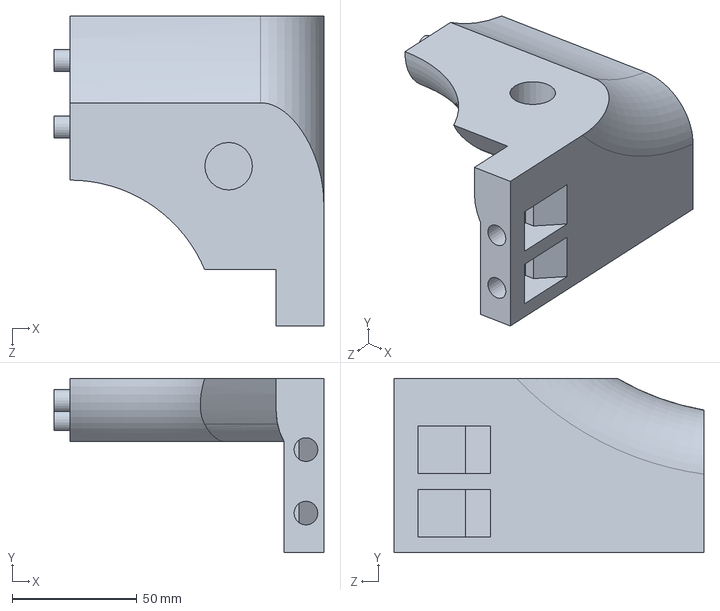
[picture p84: CAD file, 2021-04-09]
SolidWorks Files/Neck/Neck Mechanism/Neck Sizing Bottom Male.SLDPRT
107.9 x 69.8 x 124.1 mm
