ealauer/Animatronic_Research/Stewart Platform Initial Designs/base_top.dxf

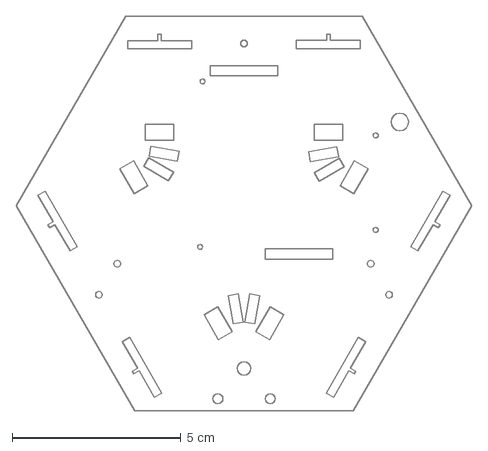
[picture p85: CAD file, 2021-04-09]
Stewart Platform Initial Designs/base_top.dxf
13.5 x 11.7 cm
