ealauer/Animatronic_Research/SolidWorks Files/Eye CAD/final_link3.SLDPRT

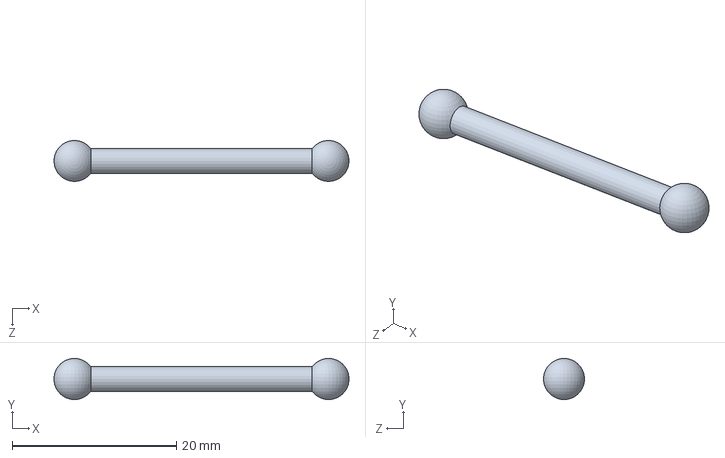
[picture p86: CAD file, 2021-04-09]
SolidWorks Files/Eye CAD/final_link3.SLDPRT
35.9 x 5.00 x 4.97 mm
