ealauer/Animatronic_Research/SolidWorks Files/Jaw/sg90-micro-servo-9g-tower-pro-1.snapshot.3/SG90 - Micro Servo 9g - Tower Pro.5.SLDPRT

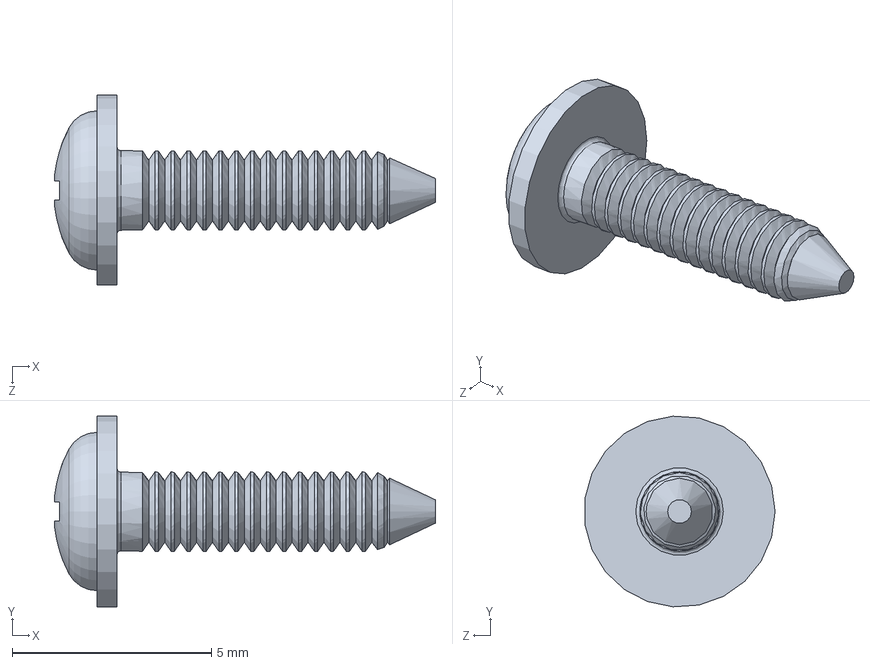
[picture p88: CAD file, 2021-04-09]
SolidWorks Files/Jaw/sg90-micro-servo-9g-tower-pro-1.snapshot.3/SG90 - Micro Servo 9g - Tower Pro.5.SLDPRT
9.57 x 4.79 x 4.78 mm
