ealauer/Animatronic_Research/SolidWorks Files/Neck/Neck Enclosure/breadboard Updated.SLDPRT

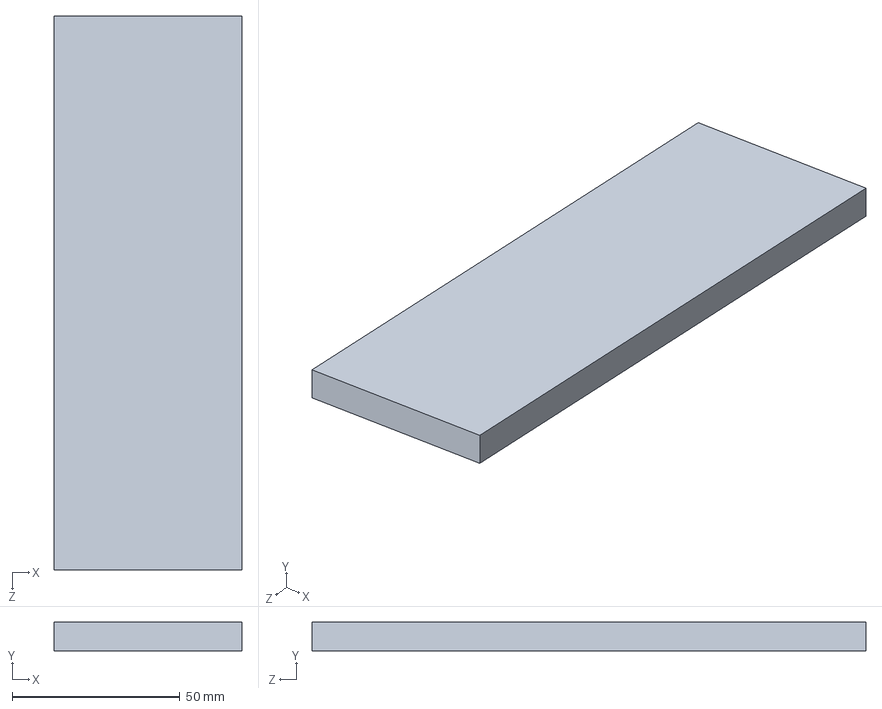
[picture p89: CAD file, 2021-04-09]
SolidWorks Files/Neck/Neck Enclosure/breadboard Updated.SLDPRT
56.0 x 8.50 x 165.0 mm
