ealauer/Animatronic_Research/SolidWorks Files/Neck/Neck Mechanism/Connecting Rod.SLDPRT

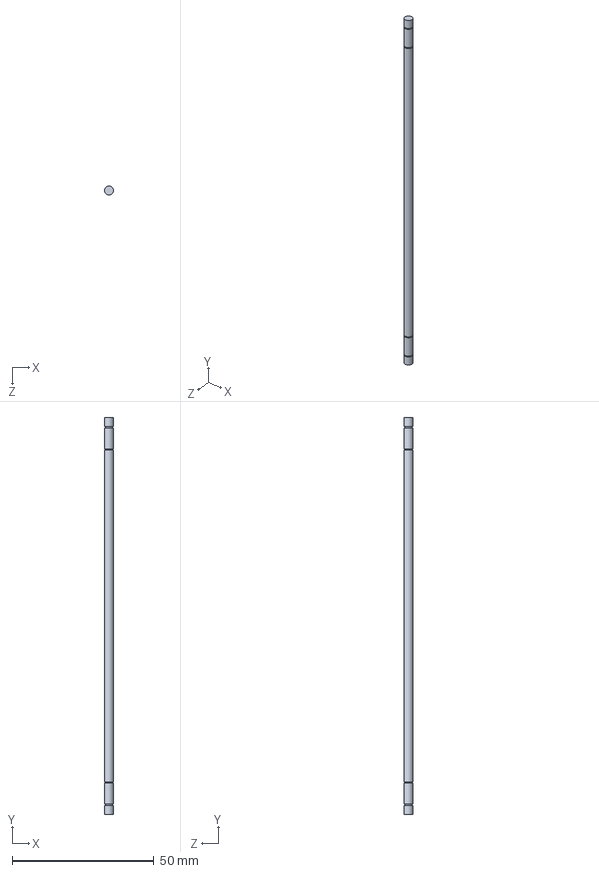
[picture p90: CAD file, 2021-04-09]
SolidWorks Files/Neck/Neck Mechanism/Connecting Rod.SLDPRT
3.17 x 140.1 x 3.17 mm
