ealauer/Animatronic_Research/Stewart Platform Initial Designs/workspace modeling V2.SLDPRT

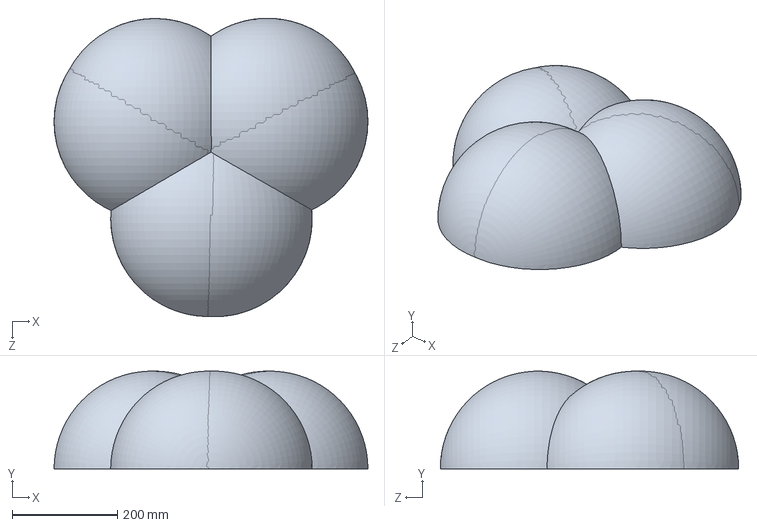
[picture p91: CAD file, 2021-04-09]
Stewart Platform Initial Designs/workspace modeling V2.SLDPRT
595.6 x 185.0 x 566.2 mm
