ealauer/Animatronic_Research/SolidWorks Files/Eye CAD/final_eye_holder_V3.75_final.SLDPRT

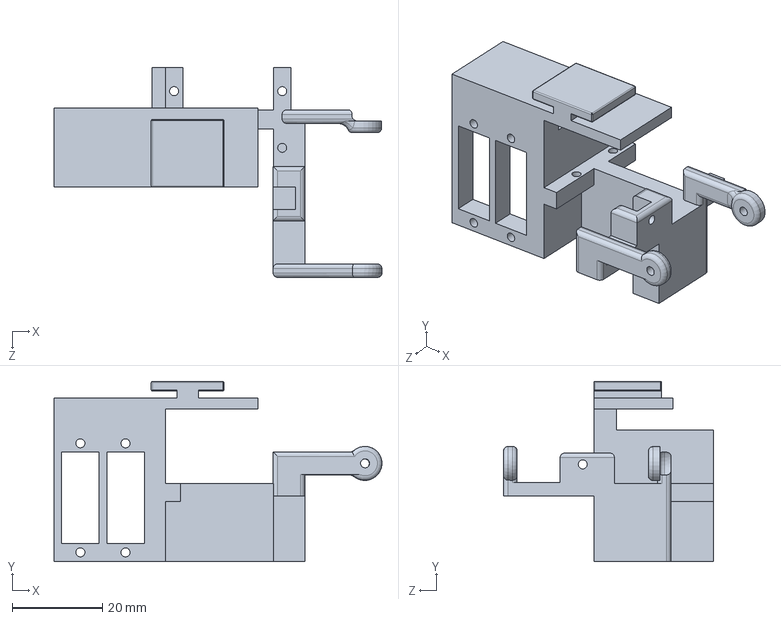
[picture p92: CAD file, 2021-04-09]
SolidWorks Files/Eye CAD/final_eye_holder_V3.75_final.SLDPRT
72.5 x 39.8 x 46.4 mm
