ealauer/Animatronic_Research/SolidWorks Files/Neck/Neck Enclosure/Stands.SLDPRT

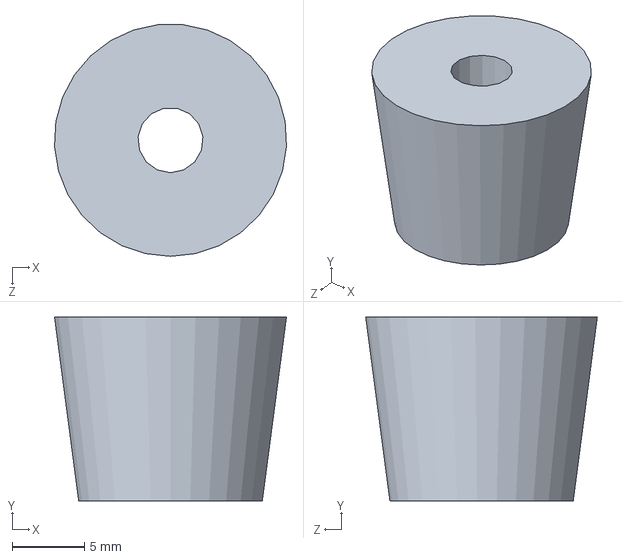
[picture p94: CAD file, 2021-04-09]
SolidWorks Files/Neck/Neck Enclosure/Stands.SLDPRT
16.0 x 12.7 x 16.0 mm
