ealauer/Animatronic_Research/SolidWorks Files/Neck/Neck Mechanism/Height Saver.SLDPRT

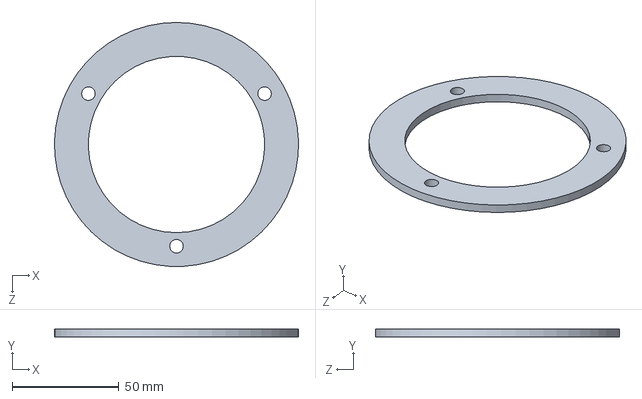
[picture p95: CAD file, 2021-04-09]
SolidWorks Files/Neck/Neck Mechanism/Height Saver.SLDPRT
114.2 x 3.81 x 114.3 mm
