ealauer/Animatronic_Research/SolidWorks Files/Stationary Base Actual V2.SLDPRT

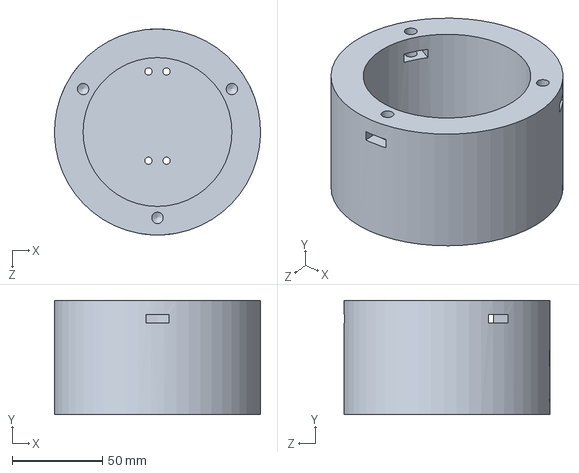
[picture p96: CAD file, 2021-04-09]
SolidWorks Files/Stationary Base Actual V2.SLDPRT
114.2 x 63.5 x 114.3 mm
