ealauer/Animatronic_Research/Stewart Platform Initial Designs/top platform filled.SLDPRT

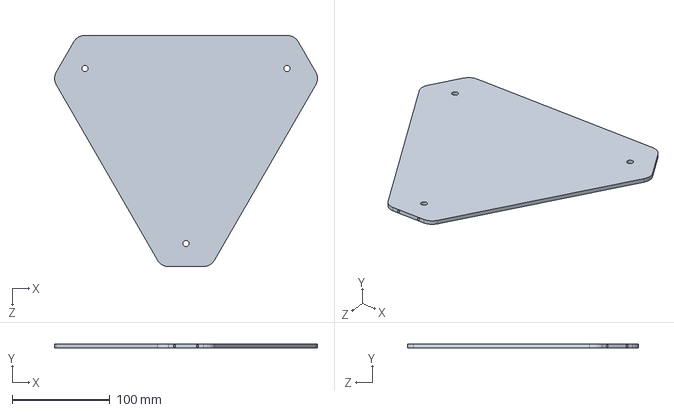
[picture p97: CAD file, 2021-04-09]
Stewart Platform Initial Designs/top platform filled.SLDPRT
269.1 x 3.81 x 236.5 mm
