ealauer/Animatronic_Research/SolidWorks Files/Eye CAD/final_servo_ball_joint_link3.SLDPRT

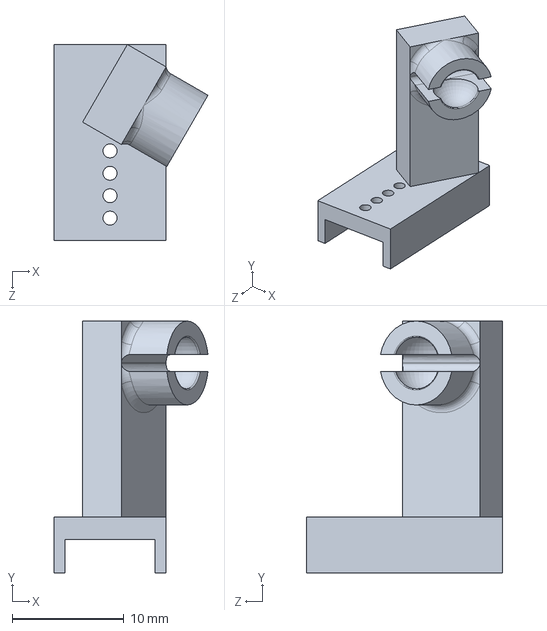
[picture p98: CAD file, 2021-04-09]
SolidWorks Files/Eye CAD/final_servo_ball_joint_link3.SLDPRT
13.7 x 22.5 x 17.5 mm
