ealauer/Animatronic_Research/SolidWorks Files/Jaw/Jaw Thrust Linkage/TriangleEditedRight.SLDPRT

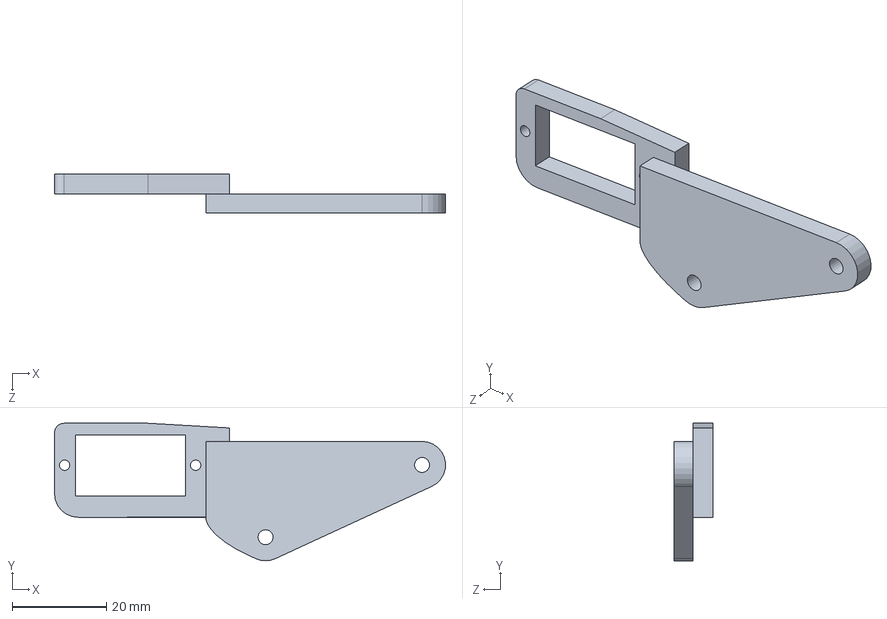
[picture p99: CAD file, 2021-04-09]
SolidWorks Files/Jaw/Jaw Thrust Linkage/TriangleEditedRight.SLDPRT
83.0 x 29.2 x 8.20 mm
