ealauer/Animatronic_Research/SolidWorks Files/Neck/Neck Enclosure/Side Plates.SLDPRT

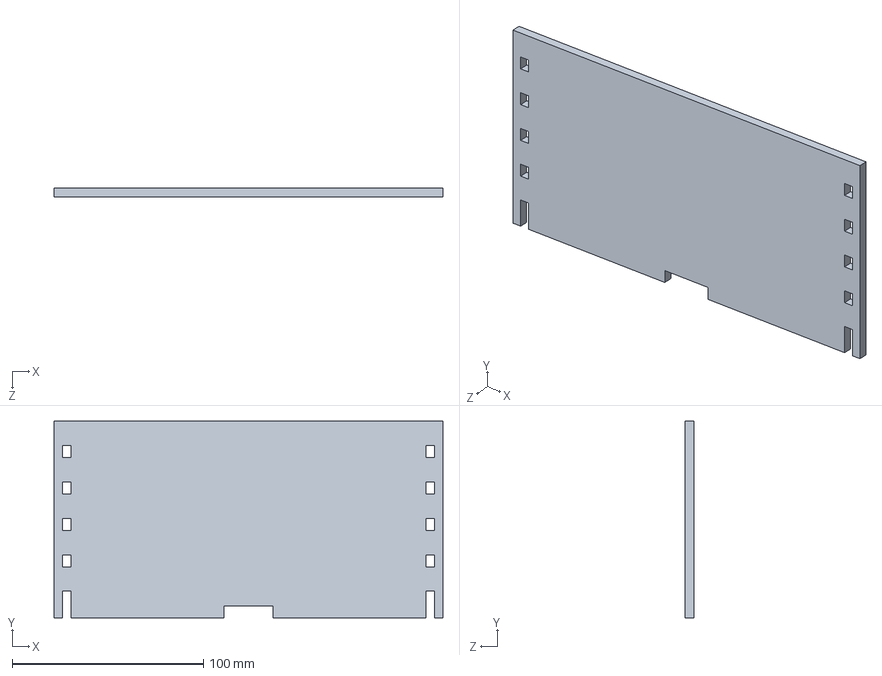
[picture p100: CAD file, 2021-04-09]
SolidWorks Files/Neck/Neck Enclosure/Side Plates.SLDPRT
203.2 x 102.9 x 4.50 mm
