ealauer/Animatronic_Research/SolidWorks Files/Neck/Neck Mechanism/Neck Sizing.SLDPRT

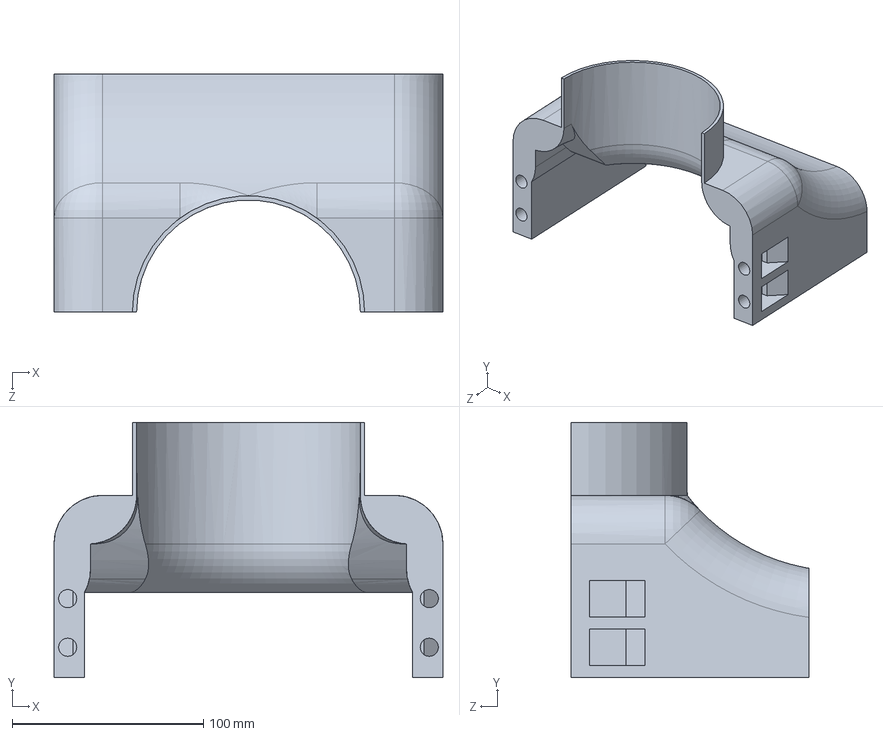
[picture p101: CAD file, 2021-04-09]
SolidWorks Files/Neck/Neck Mechanism/Neck Sizing.SLDPRT
203.2 x 133.4 x 124.1 mm
