ealauer/Animatronic_Research/SolidWorks Files/Eye CAD/final_servo_ball_joint_link4.SLDPRT

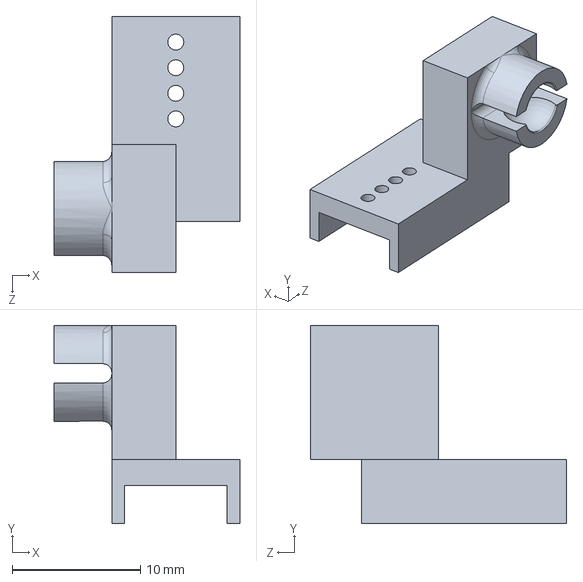
[picture p103: CAD file, 2021-04-09]
SolidWorks Files/Eye CAD/final_servo_ball_joint_link4.SLDPRT
14.5 x 15.5 x 20.0 mm
