ealauer/Animatronic_Research/SolidWorks Files/new link.SLDPRT

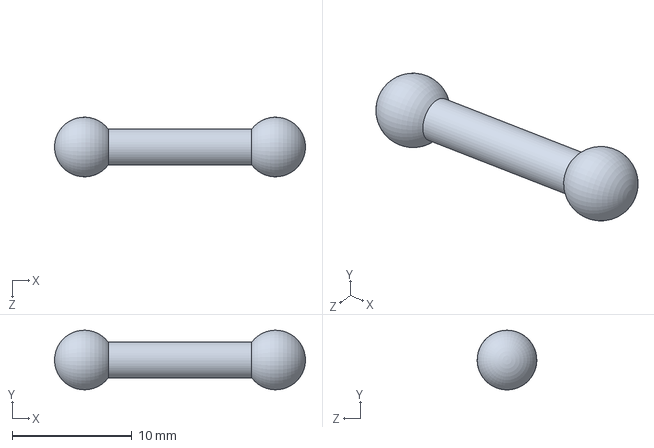
[picture p104: CAD file, 2021-04-09]
SolidWorks Files/new link.SLDPRT
21.0 x 4.99 x 4.99 mm
