ealauer/Animatronic_Research/Stewart Platform Initial Designs/servo_arm_V2.SLDPRT

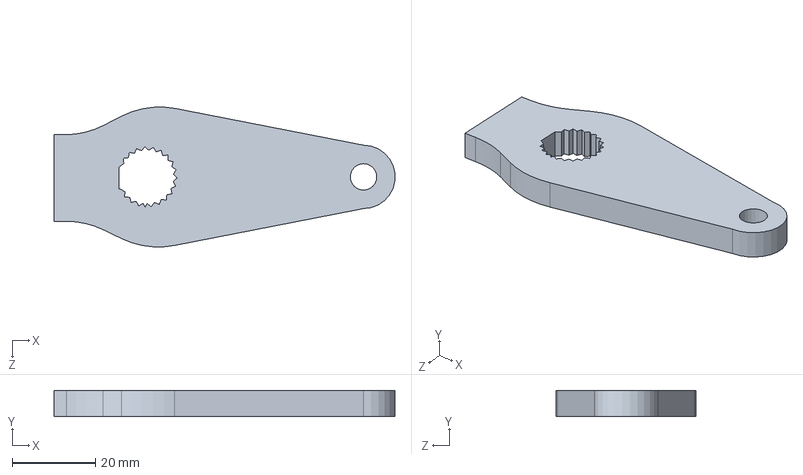
[picture p105: CAD file, 2021-04-09]
Stewart Platform Initial Designs/servo_arm_V2.SLDPRT
82.0 x 6.35 x 33.6 mm
