ealauer/Animatronic_Research/SolidWorks Files/Eye CAD/final_clip on eyelid rev3.SLDPRT

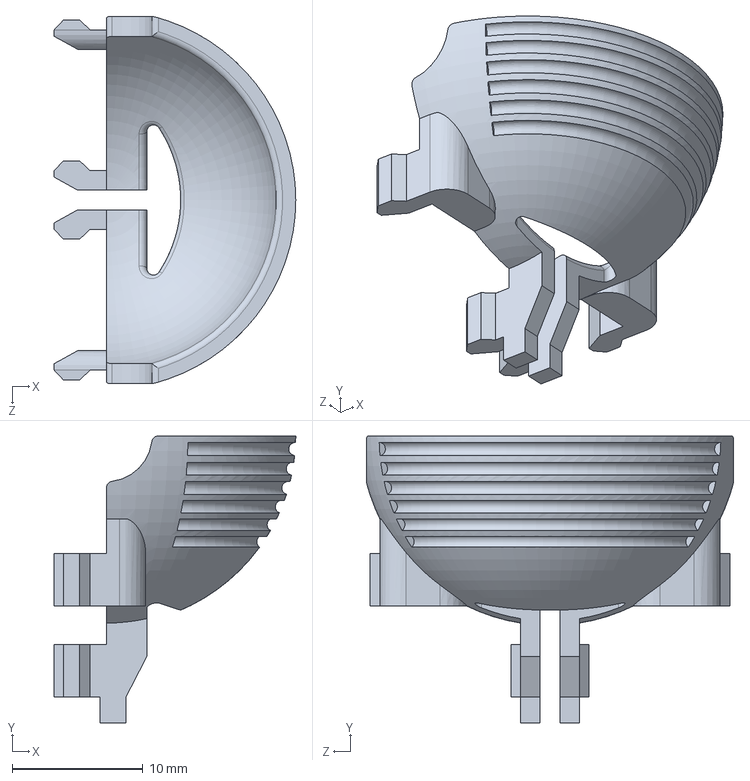
[picture p106: CAD file, 2021-04-09]
SolidWorks Files/Eye CAD/final_clip on eyelid rev3.SLDPRT
18.5 x 22.0 x 28.1 mm
