ealauer/Animatronic_Research/SolidWorks Files/Eyebrows/Left Eyebrow/drilled and trimmed servo horn.SLDPRT

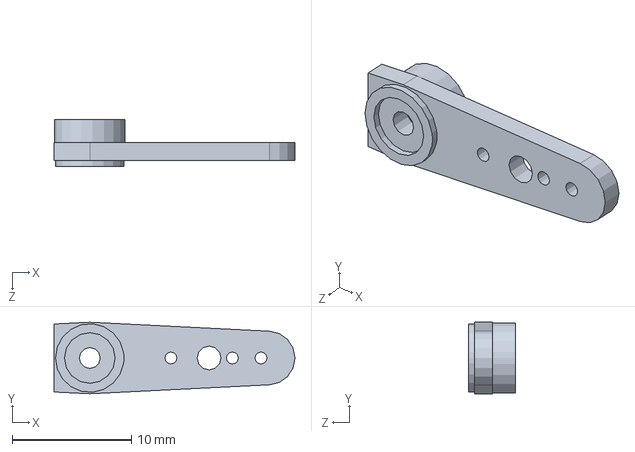
[picture p107: CAD file, 2021-04-09]
SolidWorks Files/Eyebrows/Left Eyebrow/drilled and trimmed servo horn.SLDPRT
20.2 x 6.00 x 3.90 mm
