ealauer/Animatronic_Research/SolidWorks Files/Neck/Neck Enclosure/Back Plate.SLDPRT

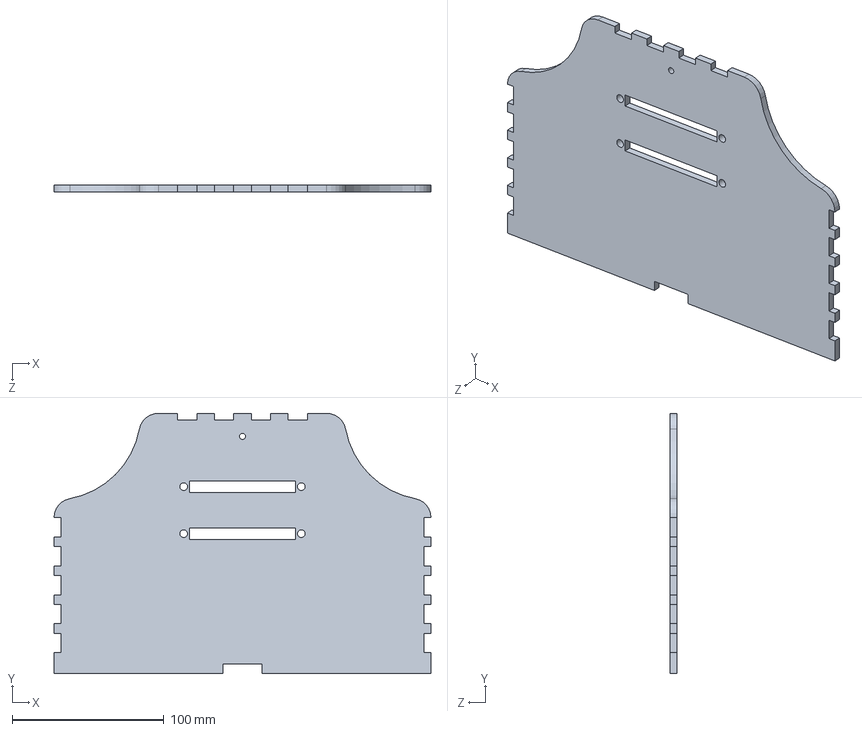
[picture p108: CAD file, 2021-04-09]
SolidWorks Files/Neck/Neck Enclosure/Back Plate.SLDPRT
248.3 x 171.4 x 4.50 mm
