ealauer/Animatronic_Research/SolidWorks Files/Neck/Neck Mechanism/Stationary Base.SLDPRT

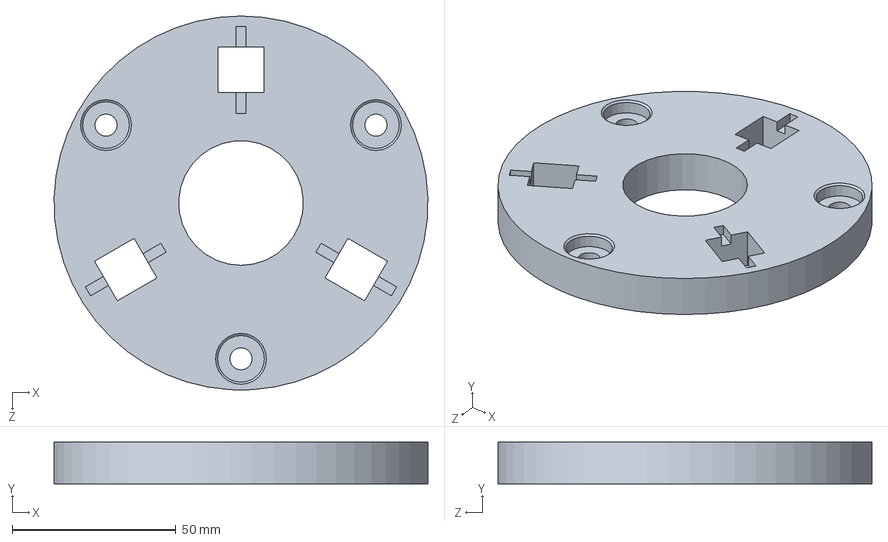
[picture p109: CAD file, 2021-04-09]
SolidWorks Files/Neck/Neck Mechanism/Stationary Base.SLDPRT
114.2 x 12.7 x 114.3 mm
