ealauer/Animatronic_Research/SolidWorks Files/Neck/Neck Mechanism/Servo Block.SLDPRT

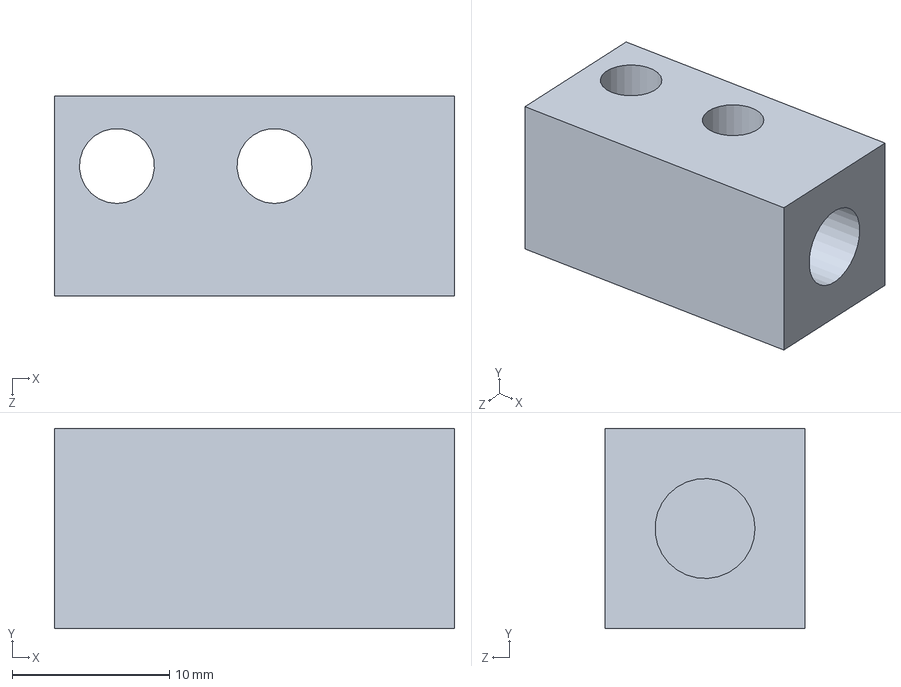
[picture p111: CAD file, 2021-04-09]
SolidWorks Files/Neck/Neck Mechanism/Servo Block.SLDPRT
25.4 x 12.7 x 12.7 mm
