ealauer/Animatronic_Research/SolidWorks Files/Shaft Servo Interface.SLDPRT

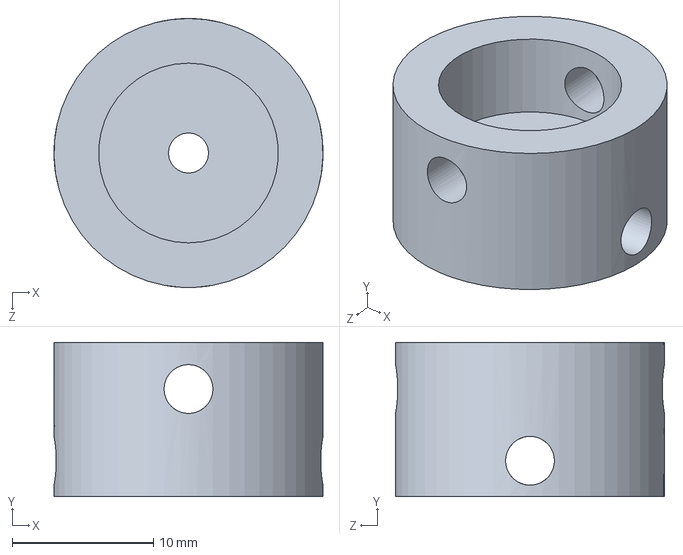
[picture p112: CAD file, 2021-04-09]
SolidWorks Files/Shaft Servo Interface.SLDPRT
19.1 x 10.9 x 19.1 mm
