ealauer/Animatronic_Research/Stewart Platform Initial Designs/base_bot.dxf

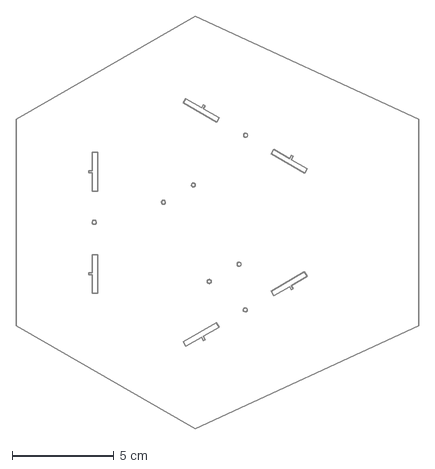
[picture p113: CAD file, 2021-04-09]
Stewart Platform Initial Designs/base_bot.dxf
19.8 x 20.3 cm
