ealauer/Animatronic_Research/SolidWorks Files/Eye CAD/platform_V3 (2).SLDPRT

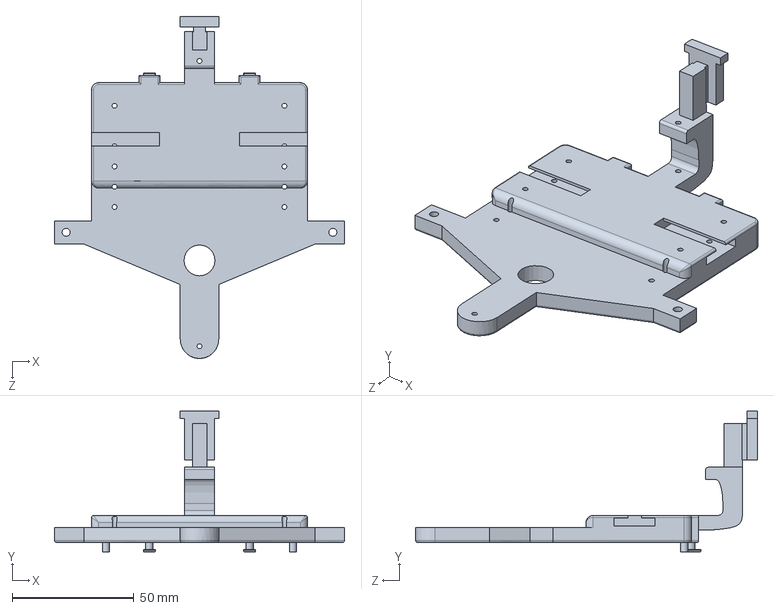
[picture p114: CAD file, 2021-04-09]
SolidWorks Files/Eye CAD/platform_V3 (2).SLDPRT
119.4 x 57.9 x 140.7 mm
