ealauer/Animatronic_Research/SolidWorks Files/Jaw/Jaw Thrust Linkage/Drivingv1.SLDPRT

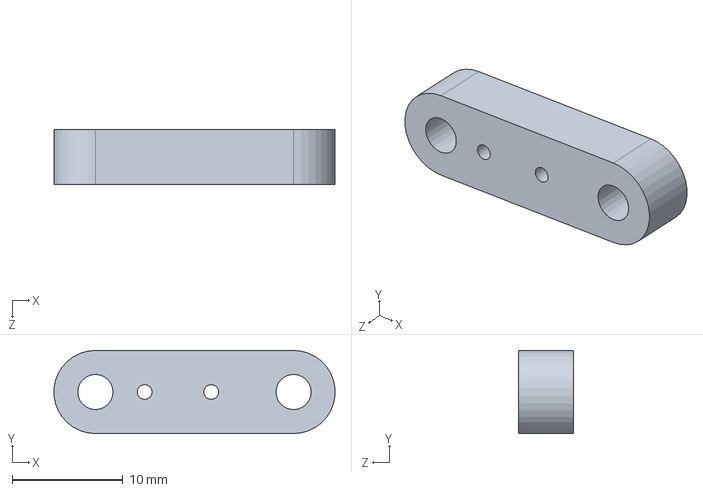
[picture p115: CAD file, 2021-04-09]
SolidWorks Files/Jaw/Jaw Thrust Linkage/Drivingv1.SLDPRT
25.3 x 7.50 x 5.00 mm
