ealauer/Animatronic_Research/SolidWorks Files/Neck/Neck Enclosure/Base.SLDPRT

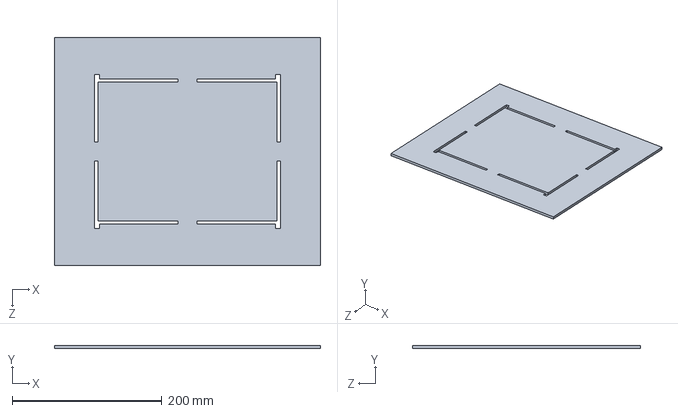
[picture p116: CAD file, 2021-04-09]
SolidWorks Files/Neck/Neck Enclosure/Base.SLDPRT
355.6 x 4.50 x 304.8 mm
