ealauer/Animatronic_Research/Stewart Platform Initial Designs/botplatformsketch.SLDPRT

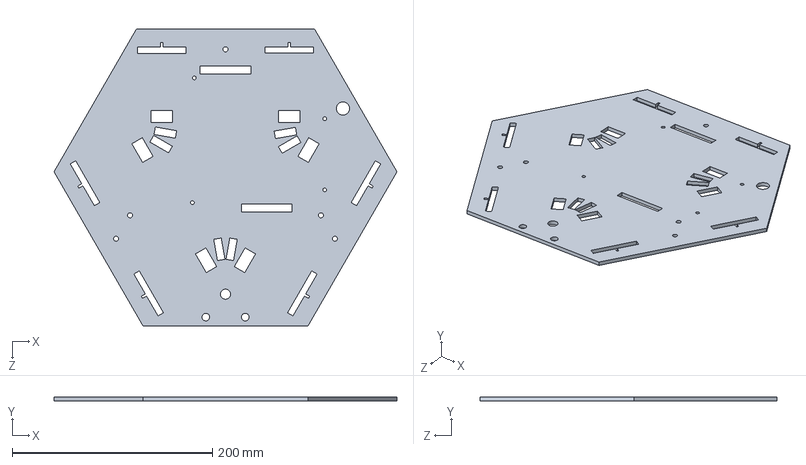
[picture p117: CAD file, 2021-04-09]
Stewart Platform Initial Designs/botplatformsketch.SLDPRT
342.4 x 3.81 x 296.5 mm
