ealauer/Animatronic_Research/SolidWorks Files/Jaw/Jaw Thrust Linkage/Driven1.SLDPRT

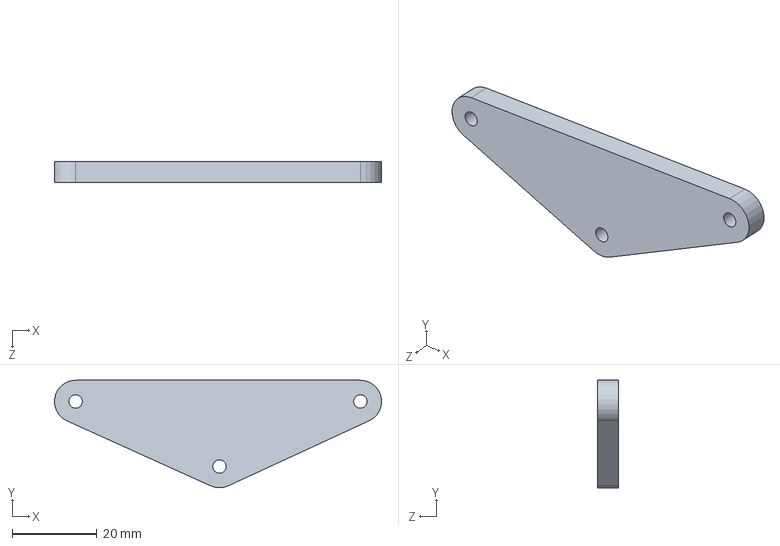
[picture p118: CAD file, 2021-04-09]
SolidWorks Files/Jaw/Jaw Thrust Linkage/Driven1.SLDPRT
77.0 x 25.3 x 5.00 mm
