ealauer/Animatronic_Research/SolidWorks Files/Neck/Neck Enclosure/SHOULDER (HOLE).SLDPRT

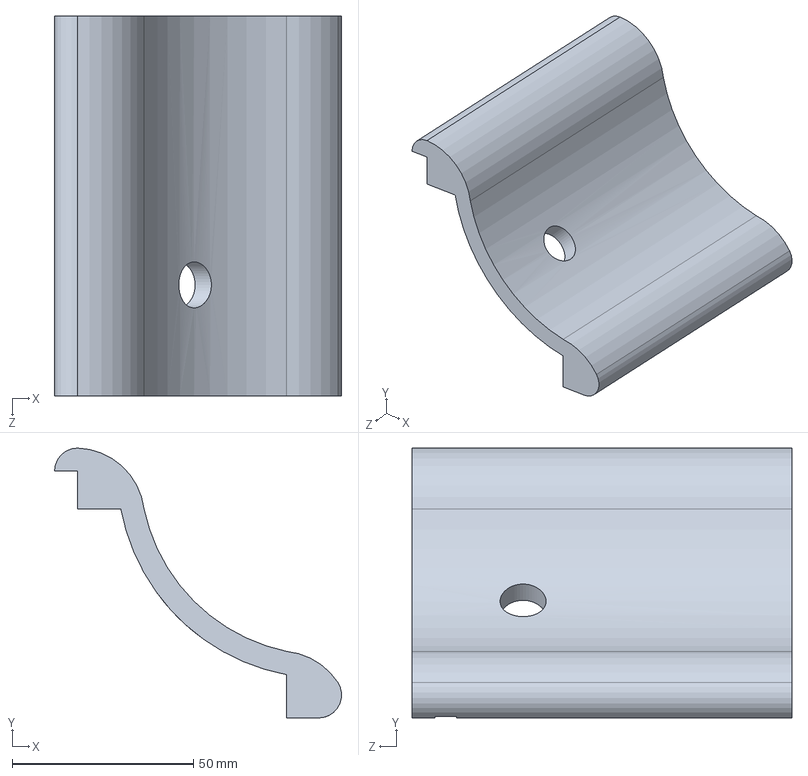
[picture p119: CAD file, 2021-04-09]
SolidWorks Files/Neck/Neck Enclosure/SHOULDER (HOLE).SLDPRT
79.2 x 74.5 x 104.8 mm
