ealauer/Animatronic_Research/Stewart Platform Initial Designs/servo_arm.SLDPRT

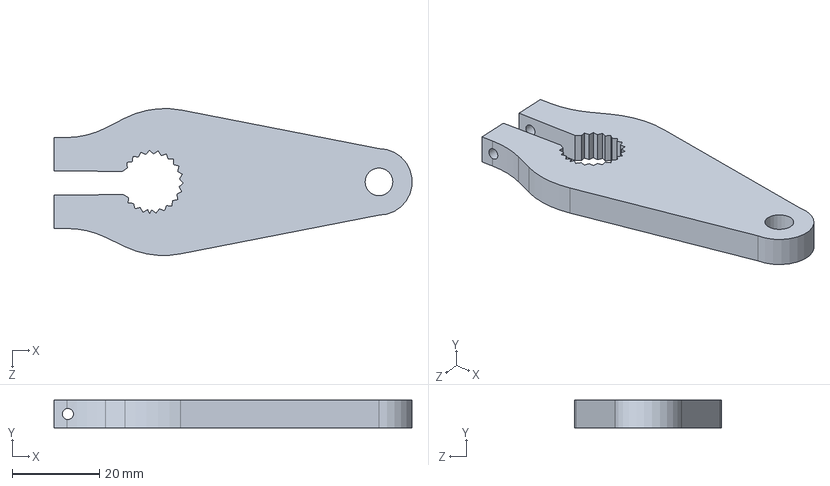
[picture p120: CAD file, 2021-04-09]
Stewart Platform Initial Designs/servo_arm.SLDPRT
82.0 x 6.35 x 33.6 mm
