ealauer/Animatronic_Research/SolidWorks Files/Eye CAD/final_servo_ball_joint_link2.SLDPRT

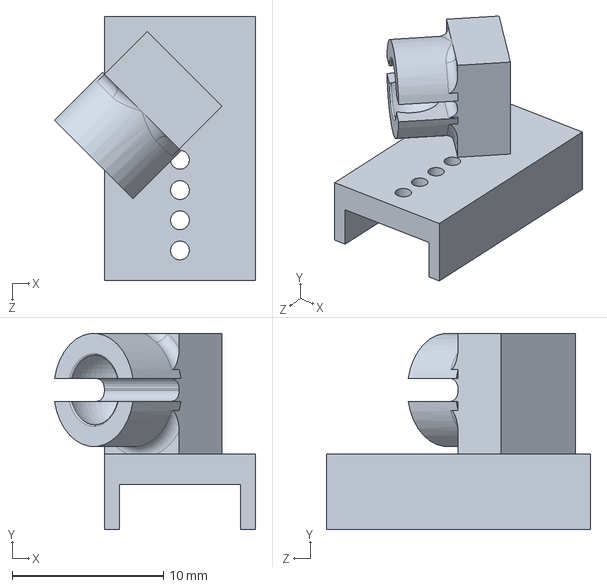
[picture p121: CAD file, 2021-04-09]
SolidWorks Files/Eye CAD/final_servo_ball_joint_link2.SLDPRT
13.3 x 13.0 x 17.5 mm
