ealauer/Animatronic_Research/SolidWorks Files/Rod Rotation.SLDPRT

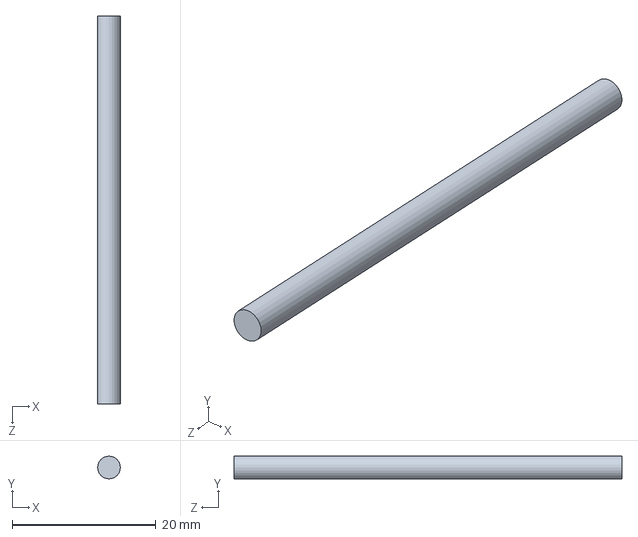
[picture p122: CAD file, 2021-04-09]
SolidWorks Files/Rod Rotation.SLDPRT
3.17 x 3.17 x 54.0 mm
