ealauer/Animatronic_Research/SolidWorks Files/Neck/Neck Mechanism/Servo Stand-In.SLDPRT

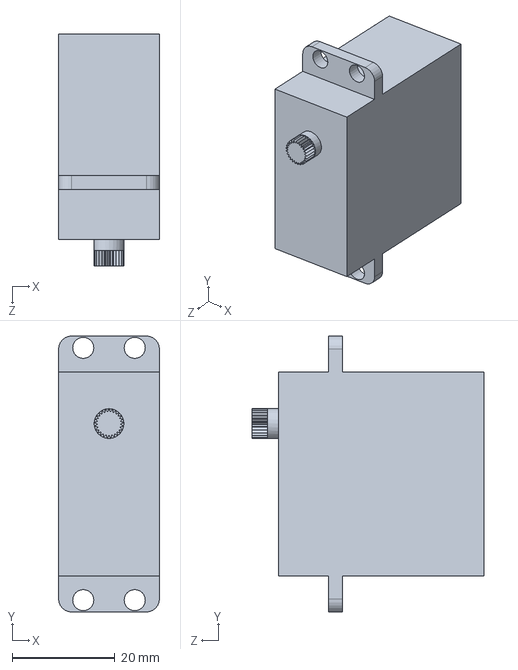
[picture p123: CAD file, 2021-04-09]
SolidWorks Files/Neck/Neck Mechanism/Servo Stand-In.SLDPRT
19.6 x 53.6 x 45.0 mm
