ealauer/Animatronic_Research/SolidWorks Files/Neck/Neck Enclosure/Front Plate.SLDPRT

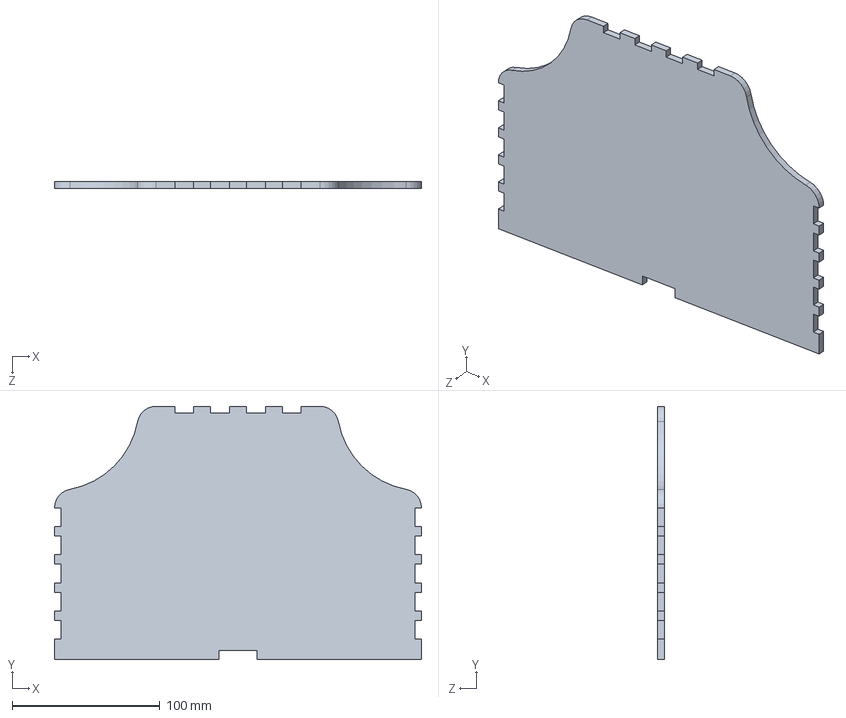
[picture p124: CAD file, 2021-04-09]
SolidWorks Files/Neck/Neck Enclosure/Front Plate.SLDPRT
248.3 x 171.4 x 4.50 mm
