ealauer/Animatronic_Research/SolidWorks Files/Rotational Saver.SLDPRT

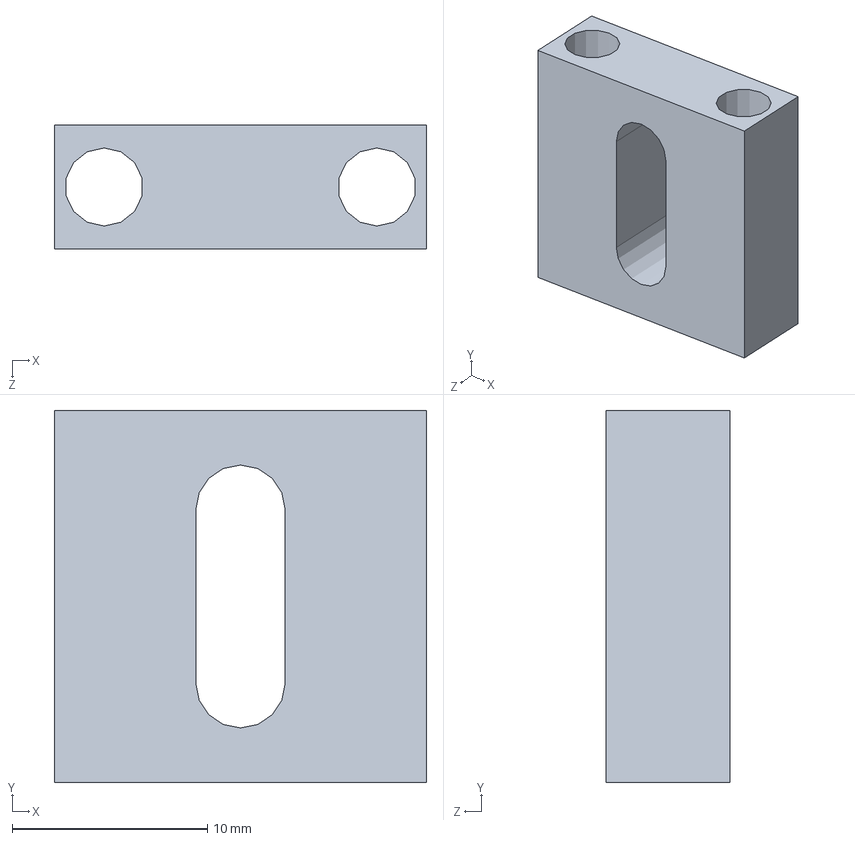
[picture p125: CAD file, 2021-04-09]
SolidWorks Files/Rotational Saver.SLDPRT
19.1 x 19.1 x 6.35 mm
