ealauer/Animatronic_Research/SolidWorks Files/Head Neck Interface.SLDPRT

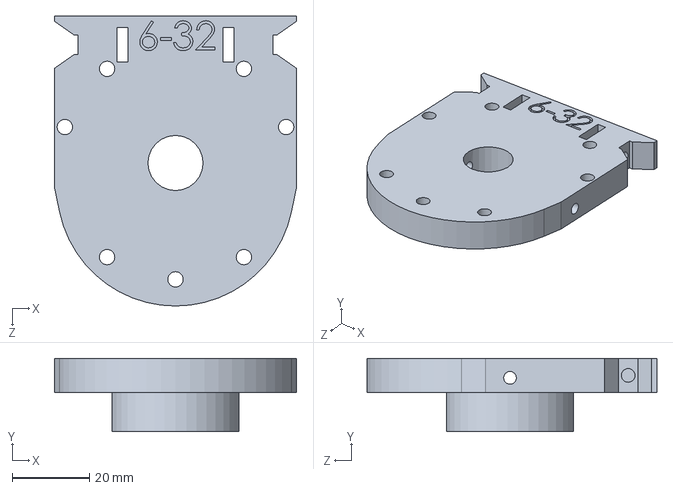
[picture p126: CAD file, 2021-04-09]
SolidWorks Files/Head Neck Interface.SLDPRT
62.7 x 19.0 x 75.2 mm
