ealauer/Animatronic_Research/SolidWorks Files/Neck/Neck Enclosure/Top.SLDPRT

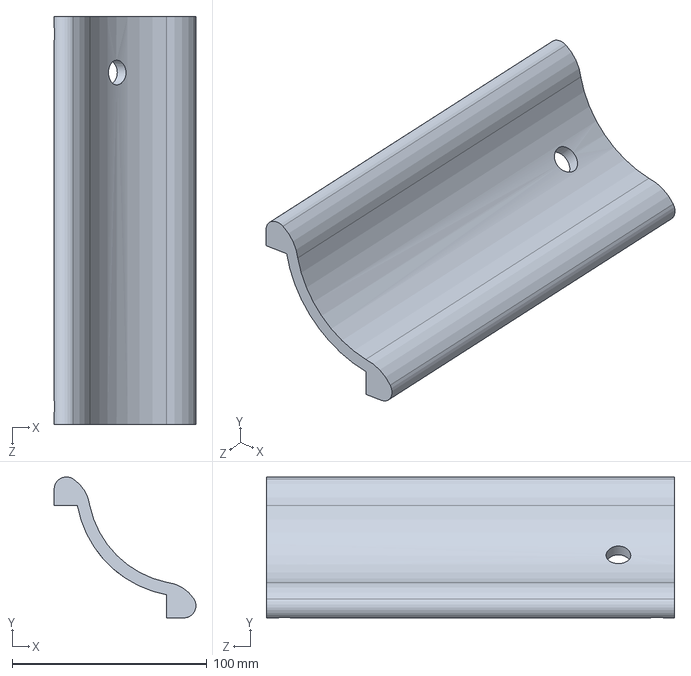
[picture p127: CAD file, 2021-04-09]
SolidWorks Files/Neck/Neck Enclosure/Top.SLDPRT
72.9 x 72.4 x 209.5 mm
