ealauer/Animatronic_Research/SolidWorks Files/Neck/Neck Mechanism/U-Joint to Central Shaft Rod.SLDPRT

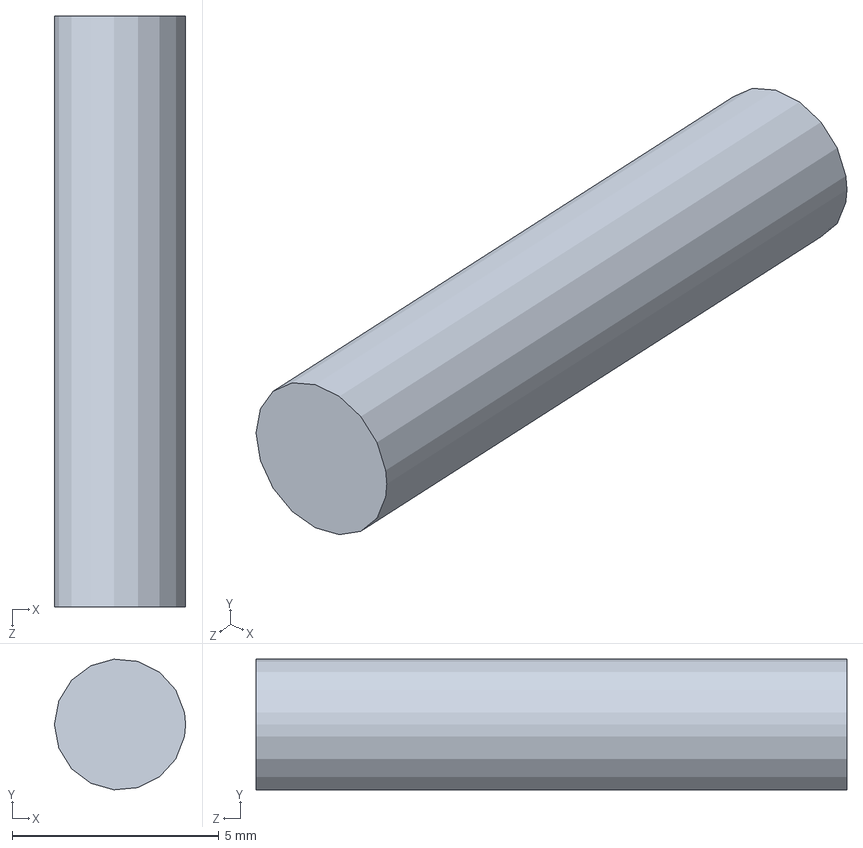
[picture p128: CAD file, 2021-04-09]
SolidWorks Files/Neck/Neck Mechanism/U-Joint to Central Shaft Rod.SLDPRT
3.17 x 3.16 x 14.3 mm
