ealauer/Animatronic_Research/SolidWorks Files/Eye CAD/final_link1.SLDPRT

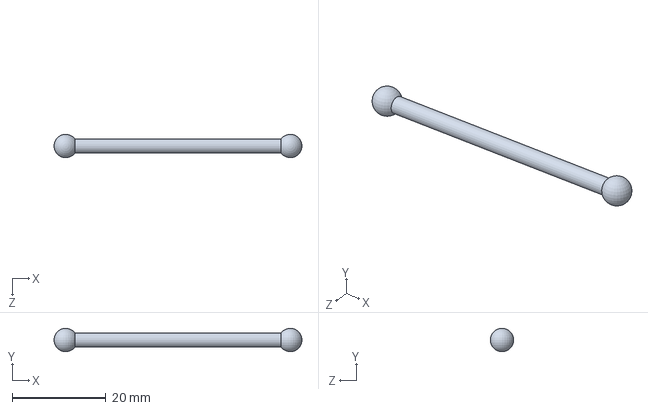
[picture p129: CAD file, 2021-04-09]
SolidWorks Files/Eye CAD/final_link1.SLDPRT
53.0 x 5.00 x 5.00 mm
