ealauer/Animatronic_Research/SolidWorks Files/Neck/Neck Mechanism/Moving Neck Assembly.JPG

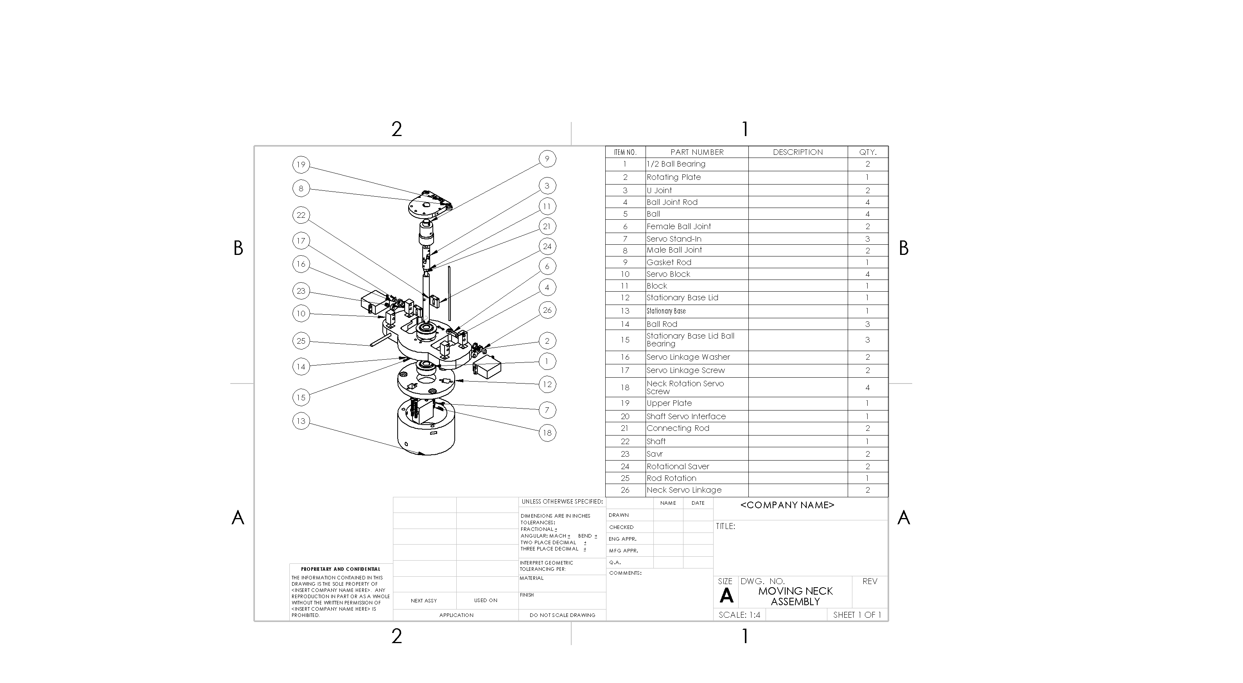
SolidWorks Files/Neck/Neck Mechanism/Moving Neck Assembly.JPG
